x893/Thingy52/documentation/dfu_mode.png

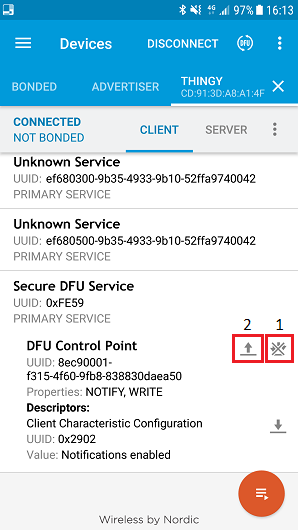
documentation/dfu_mode.png
