x893/Thingy52/documentation/distribution_packet.png

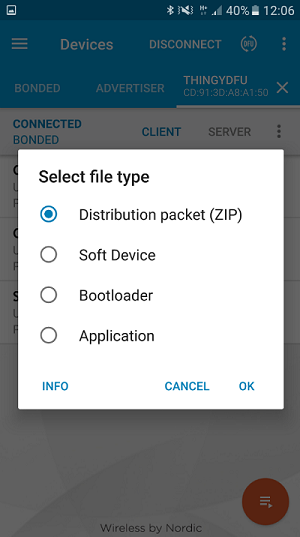
documentation/distribution_packet.png
