x893/Thingy52/documentation/fe59.png

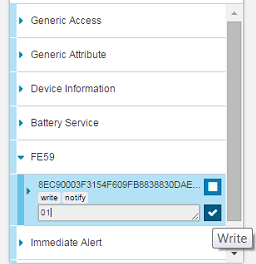
documentation/fe59.png
