x893/Thingy52/documentation/firmware_cable.png

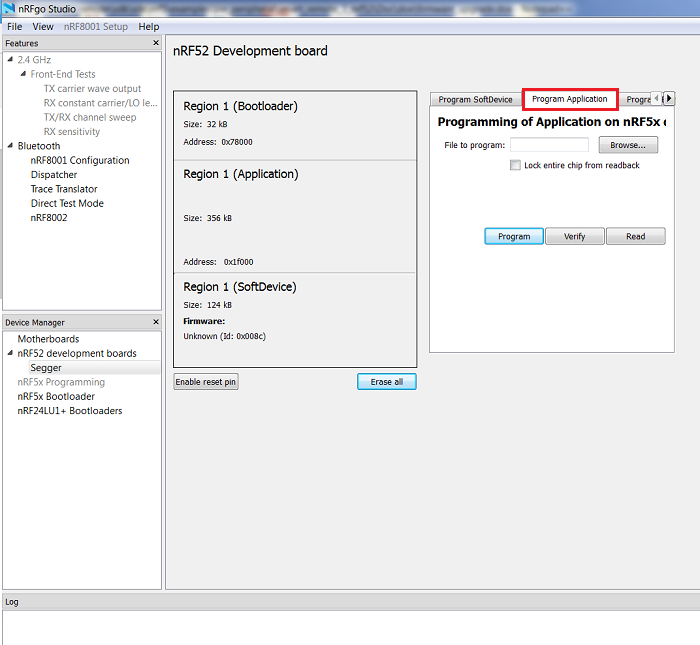
documentation/firmware_cable.png
