x893/Thingy52/documentation/firmware_update.png

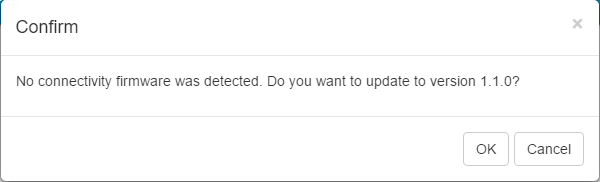
documentation/firmware_update.png
