x893/Thingy52/documentation/keil1.png

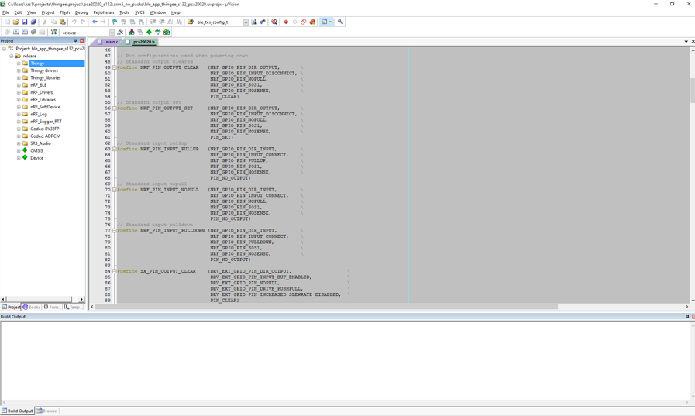
documentation/keil1.png
