x893/Thingy52/documentation/thingy_firmware_arch.png

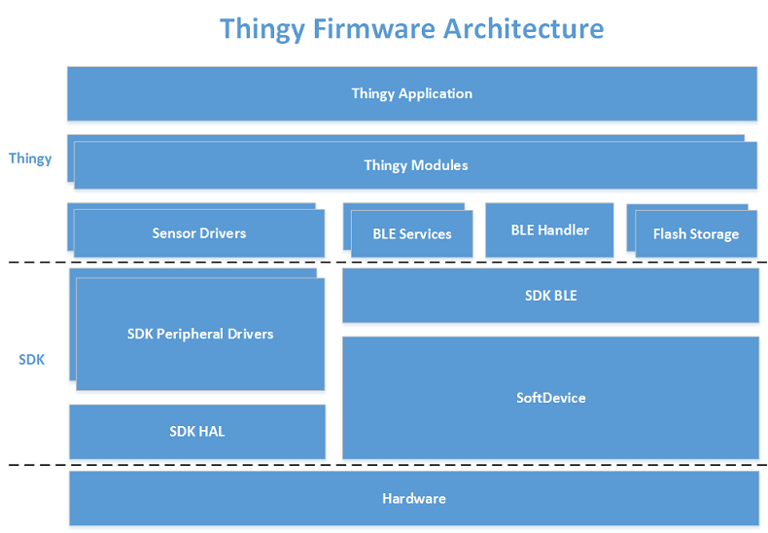
documentation/thingy_firmware_arch.png
