x893/Thingy52/sdk_components/drivers_nrf/uart/nrf_drv_uart.h

#define NRF_DRV_UART_H
#include "nrf_uart.h"
#ifdef UARTE_PRESENT
#include "nrf_uarte.h"
#endif
#include "sdk_errors.h"
#include "sdk_config.h"
#ifdef __cplusplus
extern "C" {
#endif
#define UART0_INSTANCE_INDEX 0
#define UART_COUNT 1
#if defined(UARTE_PRESENT)
    #define NRF_DRV_UART_PERIPHERAL(id)           \
        (CONCAT_3(UART, id, _CONFIG_USE_EASY_DMA) == 1 ? \
            (void *)CONCAT_2(NRF_UARTE, id)       \
          : (void *)CONCAT_2(NRF_UART, id))
#else
    #define NRF_DRV_UART_PERIPHERAL(id)  (void *)CONCAT_2(NRF_UART, id)
#endif
#if defined(UARTE_PRESENT)
#if (UART_EASY_DMA_SUPPORT == 1)
#define UARTE_IN_USE
#endif
#if (UART_LEGACY_SUPPORT == 1)
#define UART_IN_USE
#endif
#if (UART_ENABLED == 1) && ((!defined(UARTE_IN_USE) && !defined(UART_IN_USE)) || ((UART_EASY_DMA_SUPPORT == 0) && (UART_LEGACY_SUPPORT == 0)))
#error "Illegal settings in uart module!"
#endif
#elif defined(UART_PRESENT)
#define UART_IN_USE
#endif
typedef struct
{
    union
    {
#if (defined(UARTE_IN_USE))
    NRF_UARTE_Type * p_uarte; ///< Pointer to a structure with UARTE registers.
#endif
#if (defined(UART_IN_USE) || (UART_ENABLED == 0))
    NRF_UART_Type * p_uart;   ///< Pointer to a structure with UART registers.
#endif
    } reg;
    uint8_t drv_inst_idx;     ///< Driver instance index.
} nrf_drv_uart_t;
#define NRF_DRV_UART_INSTANCE(id)                            \
{                                                            \
    .reg          = {NRF_DRV_UART_PERIPHERAL(id)},           \
    .drv_inst_idx = CONCAT_3(UART, id, _INSTANCE_INDEX),\
}
typedef enum
{
    NRF_DRV_UART_EVT_TX_DONE, ///< Requested TX transfer completed.
    NRF_DRV_UART_EVT_RX_DONE, ///< Requested RX transfer completed.
    NRF_DRV_UART_EVT_ERROR,   ///< Error reported by UART peripheral.
} nrf_drv_uart_evt_type_t;
typedef struct
{
    uint32_t            pseltxd;            ///< TXD pin number.
    uint32_t            pselrxd;            ///< RXD pin number.
    uint32_t            pselcts;            ///< CTS pin number.
    uint32_t            pselrts;            ///< RTS pin number.
    void *              p_context;          ///< Context passed to interrupt handler.
    nrf_uart_hwfc_t     hwfc;               ///< Flow control configuration.
    nrf_uart_parity_t   parity;             ///< Parity configuration.
    nrf_uart_baudrate_t baudrate;           ///< Baudrate.
    uint8_t             interrupt_priority; ///< Interrupt priority.
#ifdef UARTE_PRESENT
    bool                use_easy_dma;
#endif
} nrf_drv_uart_config_t;
#ifdef UARTE_PRESENT
#if !UART_LEGACY_SUPPORT
#define DEFAULT_CONFIG_USE_EASY_DMA true
#elif !UART_EASY_DMA_SUPPORT
#define DEFAULT_CONFIG_USE_EASY_DMA false
#else
#define DEFAULT_CONFIG_USE_EASY_DMA UART0_USE_EASY_DMA
#endif
#define NRF_DRV_UART_DEFAULT_CONFIG                                                   \
    {                                                                                 \
        .pseltxd            = NRF_UART_PSEL_DISCONNECTED,                             \
        .pselrxd            = NRF_UART_PSEL_DISCONNECTED,                             \
        .pselcts            = NRF_UART_PSEL_DISCONNECTED,                             \
        .pselrts            = NRF_UART_PSEL_DISCONNECTED,                             \
        .p_context          = NULL,                                                   \
        .hwfc               = (nrf_uart_hwfc_t)UART_DEFAULT_CONFIG_HWFC,              \
        .parity             = (nrf_uart_parity_t)UART_DEFAULT_CONFIG_PARITY,          \
        .baudrate           = (nrf_uart_baudrate_t)UART_DEFAULT_CONFIG_BAUDRATE,      \
        .interrupt_priority = UART_DEFAULT_CONFIG_IRQ_PRIORITY,                       \
        .use_easy_dma       = true                                                    \
    }
#else
#define NRF_DRV_UART_DEFAULT_CONFIG                                                   \
    {                                                                                 \
        .pseltxd            = NRF_UART_PSEL_DISCONNECTED,                             \
        .pselrxd            = NRF_UART_PSEL_DISCONNECTED,                             \
        .pselcts            = NRF_UART_PSEL_DISCONNECTED,                             \
        .pselrts            = NRF_UART_PSEL_DISCONNECTED,                             \
        .p_context          = NULL,                                                   \
        .hwfc               = (nrf_uart_hwfc_t)UART_DEFAULT_CONFIG_HWFC,              \
        .parity             = (nrf_uart_parity_t)UART_DEFAULT_CONFIG_PARITY,          \
        .baudrate           = (nrf_uart_baudrate_t)UART_DEFAULT_CONFIG_BAUDRATE,      \
        .interrupt_priority = UART_DEFAULT_CONFIG_IRQ_PRIORITY,                       \
    }
#endif
typedef struct
{
    uint8_t * p_data; ///< Pointer to memory used for transfer.
    uint8_t   bytes;  ///< Number of bytes transfered.
} nrf_drv_uart_xfer_evt_t;
typedef struct
{
    nrf_drv_uart_xfer_evt_t rxtx;      ///< Transfer details includes number of bytes transfered.
    uint32_t                error_mask;///< Mask of error flags that generated the event.
} nrf_drv_uart_error_evt_t;
typedef struct
{
    nrf_drv_uart_evt_type_t type;      ///< Event type.
    union
    {
        nrf_drv_uart_xfer_evt_t  rxtx; ///< Data provided for transfer completion events.
        nrf_drv_uart_error_evt_t error;///< Data provided for error event.
    } data;
} nrf_drv_uart_event_t;
typedef void (*nrf_uart_event_handler_t)(nrf_drv_uart_event_t * p_event, void * p_context);
ret_code_t nrf_drv_uart_init(nrf_drv_uart_t const *        p_instance,
                             nrf_drv_uart_config_t const * p_config,
                             nrf_uart_event_handler_t      event_handler);
void nrf_drv_uart_uninit(nrf_drv_uart_t const * p_instance);
__STATIC_INLINE uint32_t nrf_drv_uart_task_address_get(nrf_drv_uart_t const * p_instance,
                                                       nrf_uart_task_t task);
__STATIC_INLINE uint32_t nrf_drv_uart_event_address_get(nrf_drv_uart_t const * p_instance,
                                                        nrf_uart_event_t event);
ret_code_t nrf_drv_uart_tx(nrf_drv_uart_t const * p_instance,
                           uint8_t const * const p_data, uint8_t length);
bool nrf_drv_uart_tx_in_progress(nrf_drv_uart_t const * p_instance);
void nrf_drv_uart_tx_abort(nrf_drv_uart_t const * p_instance);
ret_code_t nrf_drv_uart_rx(nrf_drv_uart_t const * p_instance,
                           uint8_t * p_data, uint8_t length);
void nrf_drv_uart_rx_enable(nrf_drv_uart_t const * p_instance);
void nrf_drv_uart_rx_disable(nrf_drv_uart_t const * p_instance);
void nrf_drv_uart_rx_abort(nrf_drv_uart_t const * p_instance);
uint32_t nrf_drv_uart_errorsrc_get(nrf_drv_uart_t const * p_instance);
#ifndef SUPPRESS_INLINE_IMPLEMENTATION
__STATIC_INLINE uint32_t nrf_drv_uart_task_address_get(nrf_drv_uart_t const * p_instance,
                                                       nrf_uart_task_t task)
{
#ifdef UART_IN_USE
    return nrf_uart_task_address_get(p_instance->reg.p_uart, task);
#else
    return nrf_uarte_task_address_get(p_instance->reg.p_uarte, (nrf_uarte_task_t)task);
#endif
}
__STATIC_INLINE uint32_t nrf_drv_uart_event_address_get(nrf_drv_uart_t const * p_instance,
                                                        nrf_uart_event_t event)
{
#ifdef UART_IN_USE
    return nrf_uart_event_address_get(p_instance->reg.p_uart, event);
#else
    return nrf_uarte_event_address_get(p_instance->reg.p_uarte, (nrf_uarte_event_t)event);
#endif
}
#endif //SUPPRESS_INLINE_IMPLEMENTATION
#ifdef __cplusplus
}
#endif
