x893/Thingy52/include/drivers/drv_sx1509_bitfields.h

/*
  Copyright (c) 2010 - 2017, Nordic Semiconductor ASA
  All rights reserved.

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
  1. Redistributions of source code must retain the above copyright notice, this
     list of conditions and the following disclaimer.

  2. Redistributions in binary form, except as embedded into a Nordic
     Semiconductor ASA integrated circuit in a product or a software update for
     such product, must reproduce the above copyright notice, this list of
     conditions and the following disclaimer in the documentation and/or other
     materials provided with the distribution.

  3. Neither the name of Nordic Semiconductor ASA nor the names of its
     contributors may be used to endorse or promote products derived from this
     software without specific prior written permission.

  4. This software, with or without modification, must only be used with a
     Nordic Semiconductor ASA integrated circuit.

  5. Any software provided in binary form under this license must not be reverse
     engineered, decompiled, modified and/or disassembled.

  THIS SOFTWARE IS PROVIDED BY NORDIC SEMICONDUCTOR ASA "AS IS" AND ANY EXPRESS
  OR IMPLIED WARRANTIES, INCLUDING, BUT NOT LIMITED TO, THE IMPLIED WARRANTIES
  OF MERCHANTABILITY, NONINFRINGEMENT, AND FITNESS FOR A PARTICULAR PURPOSE ARE
  DISCLAIMED. IN NO EVENT SHALL NORDIC SEMICONDUCTOR ASA OR CONTRIBUTORS BE
  LIABLE FOR ANY DIRECT, INDIRECT, INCIDENTAL, SPECIAL, EXEMPLARY, OR
  CONSEQUENTIAL DAMAGES (INCLUDING, BUT NOT LIMITED TO, PROCUREMENT OF SUBSTITUTE
  GOODS OR SERVICES; LOSS OF USE, DATA, OR PROFITS; OR BUSINESS INTERRUPTION)
  HOWEVER CAUSED AND ON ANY THEORY OF LIABILITY, WHETHER IN CONTRACT, STRICT
  LIABILITY, OR TORT (INCLUDING NEGLIGENCE OR OTHERWISE) ARISING IN ANY WAY OUT
  OF THE USE OF THIS SOFTWARE, EVEN IF ADVISED OF THE POSSIBILITY OF SUCH DAMAGE.
 */

#ifndef DRV_SX1509_BITFIELDS_H__
#define DRV_SX1509_BITFIELDS_H__

#define DRV_SX1509_FADE_SUPPORTED_PORT_MASK (0xF0F0)

/* Register: INPBUFDISABLE. */
/* Description: Input buffer disable register. */


/* Field INPBUF15: Disables/Enables the input buffer of the I/O pin. */
#define DRV_SX1509_INPBUFDISABLE_INPBUF15_Pos      (15)                                           /*!< The position of the field. */
#define DRV_SX1509_INPBUFDISABLE_INPBUF15_Msk      (0x1 << DRV_SX1509_INPBUFDISABLE_INPBUF15_Pos) /*!< The mask of the field. */
#define DRV_SX1509_INPBUFDISABLE_INPBUF15_Disabled (0)                                            /*!< Input buffer is disabled (input actually not being used, LED connection). */
#define DRV_SX1509_INPBUFDISABLE_INPBUF15_Enabled  (1)                                            /*!< Input buffer is enabled (input actually being used). */


/* Field INPBUF14: Disables/Enables the input buffer of the I/O pin. */
#define DRV_SX1509_INPBUFDISABLE_INPBUF14_Pos      (14)                                           /*!< The position of the field. */
#define DRV_SX1509_INPBUFDISABLE_INPBUF14_Msk      (0x1 << DRV_SX1509_INPBUFDISABLE_INPBUF14_Pos) /*!< The mask of the field. */
#define DRV_SX1509_INPBUFDISABLE_INPBUF14_Disabled (0)                                            /*!< Input buffer is disabled (input actually not being used, LED connection). */
#define DRV_SX1509_INPBUFDISABLE_INPBUF14_Enabled  (1)                                            /*!< Input buffer is enabled (input actually being used). */


/* Field INPBUF13: Disables/Enables the input buffer of the I/O pin. */
#define DRV_SX1509_INPBUFDISABLE_INPBUF13_Pos      (13)                                           /*!< The position of the field. */
#define DRV_SX1509_INPBUFDISABLE_INPBUF13_Msk      (0x1 << DRV_SX1509_INPBUFDISABLE_INPBUF13_Pos) /*!< The mask of the field. */
#define DRV_SX1509_INPBUFDISABLE_INPBUF13_Disabled (0)                                            /*!< Input buffer is disabled (input actually not being used, LED connection). */
#define DRV_SX1509_INPBUFDISABLE_INPBUF13_Enabled  (1)                                            /*!< Input buffer is enabled (input actually being used). */


/* Field INPBUF12: Disables/Enables the input buffer of the I/O pin. */
#define DRV_SX1509_INPBUFDISABLE_INPBUF12_Pos      (12)                                           /*!< The position of the field. */
#define DRV_SX1509_INPBUFDISABLE_INPBUF12_Msk      (0x1 << DRV_SX1509_INPBUFDISABLE_INPBUF12_Pos) /*!< The mask of the field. */
#define DRV_SX1509_INPBUFDISABLE_INPBUF12_Disabled (0)                                            /*!< Input buffer is disabled (input actually not being used, LED connection). */
#define DRV_SX1509_INPBUFDISABLE_INPBUF12_Enabled  (1)                                            /*!< Input buffer is enabled (input actually being used). */


/* Field INPBUF11: Disables/Enables the input buffer of the I/O pin. */
#define DRV_SX1509_INPBUFDISABLE_INPBUF11_Pos      (11)                                           /*!< The position of the field. */
#define DRV_SX1509_INPBUFDISABLE_INPBUF11_Msk      (0x1 << DRV_SX1509_INPBUFDISABLE_INPBUF11_Pos) /*!< The mask of the field. */
#define DRV_SX1509_INPBUFDISABLE_INPBUF11_Disabled (0)                                            /*!< Input buffer is disabled (input actually not being used, LED connection). */
#define DRV_SX1509_INPBUFDISABLE_INPBUF11_Enabled  (1)                                            /*!< Input buffer is enabled (input actually being used). */


/* Field INPBUF10: Disables/Enables the input buffer of the I/O pin. */
#define DRV_SX1509_INPBUFDISABLE_INPBUF10_Pos      (10)                                           /*!< The position of the field. */
#define DRV_SX1509_INPBUFDISABLE_INPBUF10_Msk      (0x1 << DRV_SX1509_INPBUFDISABLE_INPBUF10_Pos) /*!< The mask of the field. */
#define DRV_SX1509_INPBUFDISABLE_INPBUF10_Disabled (0)                                            /*!< Input buffer is disabled (input actually not being used, LED connection). */
#define DRV_SX1509_INPBUFDISABLE_INPBUF10_Enabled  (1)                                            /*!< Input buffer is enabled (input actually being used). */


/* Field INPBUF9: Disables/Enables the input buffer of the I/O pin. */
#define DRV_SX1509_INPBUFDISABLE_INPBUF9_Pos      (9)                                           /*!< The position of the field. */
#define DRV_SX1509_INPBUFDISABLE_INPBUF9_Msk      (0x1 << DRV_SX1509_INPBUFDISABLE_INPBUF9_Pos) /*!< The mask of the field. */
#define DRV_SX1509_INPBUFDISABLE_INPBUF9_Disabled (0)                                           /*!< Input buffer is disabled (input actually not being used, LED connection). */
#define DRV_SX1509_INPBUFDISABLE_INPBUF9_Enabled  (1)                                           /*!< Input buffer is enabled (input actually being used). */


/* Field INPBUF8: Disables/Enables the input buffer of the I/O pin. */
#define DRV_SX1509_INPBUFDISABLE_INPBUF8_Pos      (8)                                           /*!< The position of the field. */
#define DRV_SX1509_INPBUFDISABLE_INPBUF8_Msk      (0x1 << DRV_SX1509_INPBUFDISABLE_INPBUF8_Pos) /*!< The mask of the field. */
#define DRV_SX1509_INPBUFDISABLE_INPBUF8_Disabled (0)                                           /*!< Input buffer is disabled (input actually not being used, LED connection). */
#define DRV_SX1509_INPBUFDISABLE_INPBUF8_Enabled  (1)                                           /*!< Input buffer is enabled (input actually being used). */


/* Field INPBUF7: Disables/Enables the input buffer of the I/O pin. */
#define DRV_SX1509_INPBUFDISABLE_INPBUF7_Pos      (7)                                           /*!< The position of the field. */
#define DRV_SX1509_INPBUFDISABLE_INPBUF7_Msk      (0x1 << DRV_SX1509_INPBUFDISABLE_INPBUF7_Pos) /*!< The mask of the field. */
#define DRV_SX1509_INPBUFDISABLE_INPBUF7_Disabled (0)                                           /*!< Input buffer is disabled (input actually not being used, LED connection). */
#define DRV_SX1509_INPBUFDISABLE_INPBUF7_Enabled  (1)                                           /*!< Input buffer is enabled (input actually being used). */


/* Field INPBUF6: Disables/Enables the input buffer of the I/O pin. */
#define DRV_SX1509_INPBUFDISABLE_INPBUF6_Pos      (6)                                           /*!< The position of the field. */
#define DRV_SX1509_INPBUFDISABLE_INPBUF6_Msk      (0x1 << DRV_SX1509_INPBUFDISABLE_INPBUF6_Pos) /*!< The mask of the field. */
#define DRV_SX1509_INPBUFDISABLE_INPBUF6_Disabled (0)                                           /*!< Input buffer is disabled (input actually not being used, LED connection). */
#define DRV_SX1509_INPBUFDISABLE_INPBUF6_Enabled  (1)                                           /*!< Input buffer is enabled (input actually being used). */


/* Field INPBUF5: Disables/Enables the input buffer of the I/O pin. */
#define DRV_SX1509_INPBUFDISABLE_INPBUF5_Pos      (5)                                           /*!< The position of the field. */
#define DRV_SX1509_INPBUFDISABLE_INPBUF5_Msk      (0x1 << DRV_SX1509_INPBUFDISABLE_INPBUF5_Pos) /*!< The mask of the field. */
#define DRV_SX1509_INPBUFDISABLE_INPBUF5_Disabled (0)                                           /*!< Input buffer is disabled (input actually not being used, LED connection). */
#define DRV_SX1509_INPBUFDISABLE_INPBUF5_Enabled  (1)                                           /*!< Input buffer is enabled (input actually being used). */


/* Field INPBUF4: Disables/Enables the input buffer of the I/O pin. */
#define DRV_SX1509_INPBUFDISABLE_INPBUF4_Pos      (4)                                           /*!< The position of the field. */
#define DRV_SX1509_INPBUFDISABLE_INPBUF4_Msk      (0x1 << DRV_SX1509_INPBUFDISABLE_INPBUF4_Pos) /*!< The mask of the field. */
#define DRV_SX1509_INPBUFDISABLE_INPBUF4_Disabled (0)                                           /*!< Input buffer is disabled (input actually not being used, LED connection). */
#define DRV_SX1509_INPBUFDISABLE_INPBUF4_Enabled  (1)                                           /*!< Input buffer is enabled (input actually being used). */


/* Field INPBUF3: Disables/Enables the input buffer of the I/O pin. */
#define DRV_SX1509_INPBUFDISABLE_INPBUF3_Pos      (3)                                           /*!< The position of the field. */
#define DRV_SX1509_INPBUFDISABLE_INPBUF3_Msk      (0x1 << DRV_SX1509_INPBUFDISABLE_INPBUF3_Pos) /*!< The mask of the field. */
#define DRV_SX1509_INPBUFDISABLE_INPBUF3_Disabled (0)                                           /*!< Input buffer is disabled (input actually not being used, LED connection). */
#define DRV_SX1509_INPBUFDISABLE_INPBUF3_Enabled  (1)                                           /*!< Input buffer is enabled (input actually being used). */


/* Field INPBUF2: Disables/Enables the input buffer of the I/O pin. */
#define DRV_SX1509_INPBUFDISABLE_INPBUF2_Pos      (2)                                           /*!< The position of the field. */
#define DRV_SX1509_INPBUFDISABLE_INPBUF2_Msk      (0x1 << DRV_SX1509_INPBUFDISABLE_INPBUF2_Pos) /*!< The mask of the field. */
#define DRV_SX1509_INPBUFDISABLE_INPBUF2_Disabled (0)                                           /*!< Input buffer is disabled (input actually not being used, LED connection). */
#define DRV_SX1509_INPBUFDISABLE_INPBUF2_Enabled  (1)                                           /*!< Input buffer is enabled (input actually being used). */


/* Field INPBUF1: Disables/Enables the input buffer of the I/O pin. */
#define DRV_SX1509_INPBUFDISABLE_INPBUF1_Pos      (1)                                           /*!< The position of the field. */
#define DRV_SX1509_INPBUFDISABLE_INPBUF1_Msk      (0x1 << DRV_SX1509_INPBUFDISABLE_INPBUF1_Pos) /*!< The mask of the field. */
#define DRV_SX1509_INPBUFDISABLE_INPBUF1_Disabled (0)                                           /*!< Input buffer is disabled (input actually not being used, LED connection). */
#define DRV_SX1509_INPBUFDISABLE_INPBUF1_Enabled  (1)                                           /*!< Input buffer is enabled (input actually being used). */


/* Field INPBUF0: Disables/Enables the input buffer of the I/O pin. */
#define DRV_SX1509_INPBUFDISABLE_INPBUF0_Pos      (0)                                           /*!< The position of the field. */
#define DRV_SX1509_INPBUFDISABLE_INPBUF0_Msk      (0x1 << DRV_SX1509_INPBUFDISABLE_INPBUF0_Pos) /*!< The mask of the field. */
#define DRV_SX1509_INPBUFDISABLE_INPBUF0_Disabled (0)                                           /*!< Input buffer is disabled (input actually not being used, LED connection). */
#define DRV_SX1509_INPBUFDISABLE_INPBUF0_Enabled  (1)                                           /*!< Input buffer is enabled (input actually being used). */


/* Register: LONGSLEWRATE. */
/* Description: Output buffer long slew register. */


/* Field PIN15: Enables/Disables increased slew rate of the output buffer of each [output-configured] IO. */
#define DRV_SX1509_LONGSLEWRATE_PIN15_Pos      (15)                                       /*!< The position of the field. */
#define DRV_SX1509_LONGSLEWRATE_PIN15_Msk      (0x1 << DRV_SX1509_LONGSLEWRATE_PIN15_Pos) /*!< The mask of the field. */
#define DRV_SX1509_LONGSLEWRATE_PIN15_Disabled (0)                                        /*!< Increased slew rate is disabled. */
#define DRV_SX1509_LONGSLEWRATE_PIN15_Enabled  (1)                                        /*!< Increased slew rate is enabled. */


/* Field PIN14: Enables/Disables increased slew rate of the output buffer of each [output-configured] IO. */
#define DRV_SX1509_LONGSLEWRATE_PIN14_Pos      (14)                                       /*!< The position of the field. */
#define DRV_SX1509_LONGSLEWRATE_PIN14_Msk      (0x1 << DRV_SX1509_LONGSLEWRATE_PIN14_Pos) /*!< The mask of the field. */
#define DRV_SX1509_LONGSLEWRATE_PIN14_Disabled (0)                                        /*!< Increased slew rate is disabled. */
#define DRV_SX1509_LONGSLEWRATE_PIN14_Enabled  (1)                                        /*!< Increased slew rate is enabled. */


/* Field PIN13: Enables/Disables increased slew rate of the output buffer of each [output-configured] IO. */
#define DRV_SX1509_LONGSLEWRATE_PIN13_Pos      (13)                                       /*!< The position of the field. */
#define DRV_SX1509_LONGSLEWRATE_PIN13_Msk      (0x1 << DRV_SX1509_LONGSLEWRATE_PIN13_Pos) /*!< The mask of the field. */
#define DRV_SX1509_LONGSLEWRATE_PIN13_Disabled (0)                                        /*!< Increased slew rate is disabled. */
#define DRV_SX1509_LONGSLEWRATE_PIN13_Enabled  (1)                                        /*!< Increased slew rate is enabled. */


/* Field PIN12: Enables/Disables increased slew rate of the output buffer of each [output-configured] IO. */
#define DRV_SX1509_LONGSLEWRATE_PIN12_Pos      (12)                                       /*!< The position of the field. */
#define DRV_SX1509_LONGSLEWRATE_PIN12_Msk      (0x1 << DRV_SX1509_LONGSLEWRATE_PIN12_Pos) /*!< The mask of the field. */
#define DRV_SX1509_LONGSLEWRATE_PIN12_Disabled (0)                                        /*!< Increased slew rate is disabled. */
#define DRV_SX1509_LONGSLEWRATE_PIN12_Enabled  (1)                                        /*!< Increased slew rate is enabled. */


/* Field PIN11: Enables/Disables increased slew rate of the output buffer of each [output-configured] IO. */
#define DRV_SX1509_LONGSLEWRATE_PIN11_Pos      (11)                                       /*!< The position of the field. */
#define DRV_SX1509_LONGSLEWRATE_PIN11_Msk      (0x1 << DRV_SX1509_LONGSLEWRATE_PIN11_Pos) /*!< The mask of the field. */
#define DRV_SX1509_LONGSLEWRATE_PIN11_Disabled (0)                                        /*!< Increased slew rate is disabled. */
#define DRV_SX1509_LONGSLEWRATE_PIN11_Enabled  (1)                                        /*!< Increased slew rate is enabled. */


/* Field PIN10: Enables/Disables increased slew rate of the output buffer of each [output-configured] IO. */
#define DRV_SX1509_LONGSLEWRATE_PIN10_Pos      (10)                                       /*!< The position of the field. */
#define DRV_SX1509_LONGSLEWRATE_PIN10_Msk      (0x1 << DRV_SX1509_LONGSLEWRATE_PIN10_Pos) /*!< The mask of the field. */
#define DRV_SX1509_LONGSLEWRATE_PIN10_Disabled (0)                                        /*!< Increased slew rate is disabled. */
#define DRV_SX1509_LONGSLEWRATE_PIN10_Enabled  (1)                                        /*!< Increased slew rate is enabled. */


/* Field PIN9: Enables/Disables increased slew rate of the output buffer of each [output-configured] IO. */
#define DRV_SX1509_LONGSLEWRATE_PIN9_Pos      (9)                                       /*!< The position of the field. */
#define DRV_SX1509_LONGSLEWRATE_PIN9_Msk      (0x1 << DRV_SX1509_LONGSLEWRATE_PIN9_Pos) /*!< The mask of the field. */
#define DRV_SX1509_LONGSLEWRATE_PIN9_Disabled (0)                                       /*!< Increased slew rate is disabled. */
#define DRV_SX1509_LONGSLEWRATE_PIN9_Enabled  (1)                                       /*!< Increased slew rate is enabled. */


/* Field PIN8: Enables/Disables increased slew rate of the output buffer of each [output-configured] IO. */
#define DRV_SX1509_LONGSLEWRATE_PIN8_Pos      (8)                                       /*!< The position of the field. */
#define DRV_SX1509_LONGSLEWRATE_PIN8_Msk      (0x1 << DRV_SX1509_LONGSLEWRATE_PIN8_Pos) /*!< The mask of the field. */
#define DRV_SX1509_LONGSLEWRATE_PIN8_Disabled (0)                                       /*!< Increased slew rate is disabled. */
#define DRV_SX1509_LONGSLEWRATE_PIN8_Enabled  (1)                                       /*!< Increased slew rate is enabled. */


/* Field PIN7: Enables/Disables increased slew rate of the output buffer of each [output-configured] IO. */
#define DRV_SX1509_LONGSLEWRATE_PIN7_Pos      (7)                                       /*!< The position of the field. */
#define DRV_SX1509_LONGSLEWRATE_PIN7_Msk      (0x1 << DRV_SX1509_LONGSLEWRATE_PIN7_Pos) /*!< The mask of the field. */
#define DRV_SX1509_LONGSLEWRATE_PIN7_Disabled (0)                                       /*!< Increased slew rate is disabled. */
#define DRV_SX1509_LONGSLEWRATE_PIN7_Enabled  (1)                                       /*!< Increased slew rate is enabled. */


/* Field PIN6: Enables/Disables increased slew rate of the output buffer of each [output-configured] IO. */
#define DRV_SX1509_LONGSLEWRATE_PIN6_Pos      (6)                                       /*!< The position of the field. */
#define DRV_SX1509_LONGSLEWRATE_PIN6_Msk      (0x1 << DRV_SX1509_LONGSLEWRATE_PIN6_Pos) /*!< The mask of the field. */
#define DRV_SX1509_LONGSLEWRATE_PIN6_Disabled (0)                                       /*!< Increased slew rate is disabled. */
#define DRV_SX1509_LONGSLEWRATE_PIN6_Enabled  (1)                                       /*!< Increased slew rate is enabled. */


/* Field PIN5: Enables/Disables increased slew rate of the output buffer of each [output-configured] IO. */
#define DRV_SX1509_LONGSLEWRATE_PIN5_Pos      (5)                                       /*!< The position of the field. */
#define DRV_SX1509_LONGSLEWRATE_PIN5_Msk      (0x1 << DRV_SX1509_LONGSLEWRATE_PIN5_Pos) /*!< The mask of the field. */
#define DRV_SX1509_LONGSLEWRATE_PIN5_Disabled (0)                                       /*!< Increased slew rate is disabled. */
#define DRV_SX1509_LONGSLEWRATE_PIN5_Enabled  (1)                                       /*!< Increased slew rate is enabled. */


/* Field PIN4: Enables/Disables increased slew rate of the output buffer of each [output-configured] IO. */
#define DRV_SX1509_LONGSLEWRATE_PIN4_Pos      (4)                                       /*!< The position of the field. */
#define DRV_SX1509_LONGSLEWRATE_PIN4_Msk      (0x1 << DRV_SX1509_LONGSLEWRATE_PIN4_Pos) /*!< The mask of the field. */
#define DRV_SX1509_LONGSLEWRATE_PIN4_Disabled (0)                                       /*!< Increased slew rate is disabled. */
#define DRV_SX1509_LONGSLEWRATE_PIN4_Enabled  (1)                                       /*!< Increased slew rate is enabled. */


/* Field PIN3: Enables/Disables increased slew rate of the output buffer of each [output-configured] IO. */
#define DRV_SX1509_LONGSLEWRATE_PIN3_Pos      (3)                                       /*!< The position of the field. */
#define DRV_SX1509_LONGSLEWRATE_PIN3_Msk      (0x1 << DRV_SX1509_LONGSLEWRATE_PIN3_Pos) /*!< The mask of the field. */
#define DRV_SX1509_LONGSLEWRATE_PIN3_Disabled (0)                                       /*!< Increased slew rate is disabled. */
#define DRV_SX1509_LONGSLEWRATE_PIN3_Enabled  (1)                                       /*!< Increased slew rate is enabled. */


/* Field PIN2: Enables/Disables increased slew rate of the output buffer of each [output-configured] IO. */
#define DRV_SX1509_LONGSLEWRATE_PIN2_Pos      (2)                                       /*!< The position of the field. */
#define DRV_SX1509_LONGSLEWRATE_PIN2_Msk      (0x1 << DRV_SX1509_LONGSLEWRATE_PIN2_Pos) /*!< The mask of the field. */
#define DRV_SX1509_LONGSLEWRATE_PIN2_Disabled (0)                                       /*!< Increased slew rate is disabled. */
#define DRV_SX1509_LONGSLEWRATE_PIN2_Enabled  (1)                                       /*!< Increased slew rate is enabled. */


/* Field PIN1: Enables/Disables increased slew rate of the output buffer of each [output-configured] IO. */
#define DRV_SX1509_LONGSLEWRATE_PIN1_Pos      (1)                                       /*!< The position of the field. */
#define DRV_SX1509_LONGSLEWRATE_PIN1_Msk      (0x1 << DRV_SX1509_LONGSLEWRATE_PIN1_Pos) /*!< The mask of the field. */
#define DRV_SX1509_LONGSLEWRATE_PIN1_Disabled (0)                                       /*!< Increased slew rate is disabled. */
#define DRV_SX1509_LONGSLEWRATE_PIN1_Enabled  (1)                                       /*!< Increased slew rate is enabled. */


/* Field PIN0: Enables/Disables increased slew rate of the output buffer of each [output-configured] IO. */
#define DRV_SX1509_LONGSLEWRATE_PIN0_Pos      (0)                                       /*!< The position of the field. */
#define DRV_SX1509_LONGSLEWRATE_PIN0_Msk      (0x1 << DRV_SX1509_LONGSLEWRATE_PIN0_Pos) /*!< The mask of the field. */
#define DRV_SX1509_LONGSLEWRATE_PIN0_Disabled (0)                                       /*!< Increased slew rate is disabled. */
#define DRV_SX1509_LONGSLEWRATE_PIN0_Enabled  (1)                                       /*!< Increased slew rate is enabled. */


/* Register: LOWDRIVE. */
/* Description: Output buffer low drive register. */


/* Field PIN15: Enables/Disables reduced drive of the output buffer of each [output-configured] IO. */
#define DRV_SX1509_LOWDRIVE_PIN15_Pos      (15)                                   /*!< The position of the field. */
#define DRV_SX1509_LOWDRIVE_PIN15_Msk      (0x1 << DRV_SX1509_LOWDRIVE_PIN15_Pos) /*!< The mask of the field. */
#define DRV_SX1509_LOWDRIVE_PIN15_Disabled (0)                                    /*!< Reduced drive is disabled. */
#define DRV_SX1509_LOWDRIVE_PIN15_Enabled  (1)                                    /*!< Reduced drive is enabled. */


/* Field PIN14: Enables/Disables reduced drive of the output buffer of each [output-configured] IO. */
#define DRV_SX1509_LOWDRIVE_PIN14_Pos      (14)                                   /*!< The position of the field. */
#define DRV_SX1509_LOWDRIVE_PIN14_Msk      (0x1 << DRV_SX1509_LOWDRIVE_PIN14_Pos) /*!< The mask of the field. */
#define DRV_SX1509_LOWDRIVE_PIN14_Disabled (0)                                    /*!< Reduced drive is disabled. */
#define DRV_SX1509_LOWDRIVE_PIN14_Enabled  (1)                                    /*!< Reduced drive is enabled. */


/* Field PIN13: Enables/Disables reduced drive of the output buffer of each [output-configured] IO. */
#define DRV_SX1509_LOWDRIVE_PIN13_Pos      (13)                                   /*!< The position of the field. */
#define DRV_SX1509_LOWDRIVE_PIN13_Msk      (0x1 << DRV_SX1509_LOWDRIVE_PIN13_Pos) /*!< The mask of the field. */
#define DRV_SX1509_LOWDRIVE_PIN13_Disabled (0)                                    /*!< Reduced drive is disabled. */
#define DRV_SX1509_LOWDRIVE_PIN13_Enabled  (1)                                    /*!< Reduced drive is enabled. */


/* Field PIN12: Enables/Disables reduced drive of the output buffer of each [output-configured] IO. */
#define DRV_SX1509_LOWDRIVE_PIN12_Pos      (12)                                   /*!< The position of the field. */
#define DRV_SX1509_LOWDRIVE_PIN12_Msk      (0x1 << DRV_SX1509_LOWDRIVE_PIN12_Pos) /*!< The mask of the field. */
#define DRV_SX1509_LOWDRIVE_PIN12_Disabled (0)                                    /*!< Reduced drive is disabled. */
#define DRV_SX1509_LOWDRIVE_PIN12_Enabled  (1)                                    /*!< Reduced drive is enabled. */


/* Field PIN11: Enables/Disables reduced drive of the output buffer of each [output-configured] IO. */
#define DRV_SX1509_LOWDRIVE_PIN11_Pos      (11)                                   /*!< The position of the field. */
#define DRV_SX1509_LOWDRIVE_PIN11_Msk      (0x1 << DRV_SX1509_LOWDRIVE_PIN11_Pos) /*!< The mask of the field. */
#define DRV_SX1509_LOWDRIVE_PIN11_Disabled (0)                                    /*!< Reduced drive is disabled. */
#define DRV_SX1509_LOWDRIVE_PIN11_Enabled  (1)                                    /*!< Reduced drive is enabled. */


/* Field PIN10: Enables/Disables reduced drive of the output buffer of each [output-configured] IO. */
#define DRV_SX1509_LOWDRIVE_PIN10_Pos      (10)                                   /*!< The position of the field. */
#define DRV_SX1509_LOWDRIVE_PIN10_Msk      (0x1 << DRV_SX1509_LOWDRIVE_PIN10_Pos) /*!< The mask of the field. */
#define DRV_SX1509_LOWDRIVE_PIN10_Disabled (0)                                    /*!< Reduced drive is disabled. */
#define DRV_SX1509_LOWDRIVE_PIN10_Enabled  (1)                                    /*!< Reduced drive is enabled. */


/* Field PIN9: Enables/Disables reduced drive of the output buffer of each [output-configured] IO. */
#define DRV_SX1509_LOWDRIVE_PIN9_Pos      (9)                                   /*!< The position of the field. */
#define DRV_SX1509_LOWDRIVE_PIN9_Msk      (0x1 << DRV_SX1509_LOWDRIVE_PIN9_Pos) /*!< The mask of the field. */
#define DRV_SX1509_LOWDRIVE_PIN9_Disabled (0)                                   /*!< Reduced drive is disabled. */
#define DRV_SX1509_LOWDRIVE_PIN9_Enabled  (1)                                   /*!< Reduced drive is enabled. */


/* Field PIN8: Enables/Disables reduced drive of the output buffer of each [output-configured] IO. */
#define DRV_SX1509_LOWDRIVE_PIN8_Pos      (8)                                   /*!< The position of the field. */
#define DRV_SX1509_LOWDRIVE_PIN8_Msk      (0x1 << DRV_SX1509_LOWDRIVE_PIN8_Pos) /*!< The mask of the field. */
#define DRV_SX1509_LOWDRIVE_PIN8_Disabled (0)                                   /*!< Reduced drive is disabled. */
#define DRV_SX1509_LOWDRIVE_PIN8_Enabled  (1)                                   /*!< Reduced drive is enabled. */


/* Field PIN7: Enables/Disables reduced drive of the output buffer of each [output-configured] IO. */
#define DRV_SX1509_LOWDRIVE_PIN7_Pos      (7)                                   /*!< The position of the field. */
#define DRV_SX1509_LOWDRIVE_PIN7_Msk      (0x1 << DRV_SX1509_LOWDRIVE_PIN7_Pos) /*!< The mask of the field. */
#define DRV_SX1509_LOWDRIVE_PIN7_Disabled (0)                                   /*!< Reduced drive is disabled. */
#define DRV_SX1509_LOWDRIVE_PIN7_Enabled  (1)                                   /*!< Reduced drive is enabled. */


/* Field PIN6: Enables/Disables reduced drive of the output buffer of each [output-configured] IO. */
#define DRV_SX1509_LOWDRIVE_PIN6_Pos      (6)                                   /*!< The position of the field. */
#define DRV_SX1509_LOWDRIVE_PIN6_Msk      (0x1 << DRV_SX1509_LOWDRIVE_PIN6_Pos) /*!< The mask of the field. */
#define DRV_SX1509_LOWDRIVE_PIN6_Disabled (0)                                   /*!< Reduced drive is disabled. */
#define DRV_SX1509_LOWDRIVE_PIN6_Enabled  (1)                                   /*!< Reduced drive is enabled. */


/* Field PIN5: Enables/Disables reduced drive of the output buffer of each [output-configured] IO. */
#define DRV_SX1509_LOWDRIVE_PIN5_Pos      (5)                                   /*!< The position of the field. */
#define DRV_SX1509_LOWDRIVE_PIN5_Msk      (0x1 << DRV_SX1509_LOWDRIVE_PIN5_Pos) /*!< The mask of the field. */
#define DRV_SX1509_LOWDRIVE_PIN5_Disabled (0)                                   /*!< Reduced drive is disabled. */
#define DRV_SX1509_LOWDRIVE_PIN5_Enabled  (1)                                   /*!< Reduced drive is enabled. */


/* Field PIN4: Enables/Disables reduced drive of the output buffer of each [output-configured] IO. */
#define DRV_SX1509_LOWDRIVE_PIN4_Pos      (4)                                   /*!< The position of the field. */
#define DRV_SX1509_LOWDRIVE_PIN4_Msk      (0x1 << DRV_SX1509_LOWDRIVE_PIN4_Pos) /*!< The mask of the field. */
#define DRV_SX1509_LOWDRIVE_PIN4_Disabled (0)                                   /*!< Reduced drive is disabled. */
#define DRV_SX1509_LOWDRIVE_PIN4_Enabled  (1)                                   /*!< Reduced drive is enabled. */


/* Field PIN3: Enables/Disables reduced drive of the output buffer of each [output-configured] IO. */
#define DRV_SX1509_LOWDRIVE_PIN3_Pos      (3)                                   /*!< The position of the field. */
#define DRV_SX1509_LOWDRIVE_PIN3_Msk      (0x1 << DRV_SX1509_LOWDRIVE_PIN3_Pos) /*!< The mask of the field. */
#define DRV_SX1509_LOWDRIVE_PIN3_Disabled (0)                                   /*!< Reduced drive is disabled. */
#define DRV_SX1509_LOWDRIVE_PIN3_Enabled  (1)                                   /*!< Reduced drive is enabled. */


/* Field PIN2: Enables/Disables reduced drive of the output buffer of each [output-configured] IO. */
#define DRV_SX1509_LOWDRIVE_PIN2_Pos      (2)                                   /*!< The position of the field. */
#define DRV_SX1509_LOWDRIVE_PIN2_Msk      (0x1 << DRV_SX1509_LOWDRIVE_PIN2_Pos) /*!< The mask of the field. */
#define DRV_SX1509_LOWDRIVE_PIN2_Disabled (0)                                   /*!< Reduced drive is disabled. */
#define DRV_SX1509_LOWDRIVE_PIN2_Enabled  (1)                                   /*!< Reduced drive is enabled. */


/* Field PIN1: Enables/Disables reduced drive of the output buffer of each [output-configured] IO. */
#define DRV_SX1509_LOWDRIVE_PIN1_Pos      (1)                                   /*!< The position of the field. */
#define DRV_SX1509_LOWDRIVE_PIN1_Msk      (0x1 << DRV_SX1509_LOWDRIVE_PIN1_Pos) /*!< The mask of the field. */
#define DRV_SX1509_LOWDRIVE_PIN1_Disabled (0)                                   /*!< Reduced drive is disabled. */
#define DRV_SX1509_LOWDRIVE_PIN1_Enabled  (1)                                   /*!< Reduced drive is enabled. */


/* Field PIN0: Enables/Disables reduced drive of the output buffer of each [output-configured] IO. */
#define DRV_SX1509_LOWDRIVE_PIN0_Pos      (0)                                   /*!< The position of the field. */
#define DRV_SX1509_LOWDRIVE_PIN0_Msk      (0x1 << DRV_SX1509_LOWDRIVE_PIN0_Pos) /*!< The mask of the field. */
#define DRV_SX1509_LOWDRIVE_PIN0_Disabled (0)                                   /*!< Reduced drive is disabled. */
#define DRV_SX1509_LOWDRIVE_PIN0_Enabled  (1)                                   /*!< Reduced drive is enabled. */


/* Register: PULLUP. */
/* Description: Pull-up register. */


/* Field PIN15: Enables/Disables the pull-up for each IO. */
#define DRV_SX1509_PULLUP_PIN15_Pos      (15)                                 /*!< The position of the field. */
#define DRV_SX1509_PULLUP_PIN15_Msk      (0x1 << DRV_SX1509_PULLUP_PIN15_Pos) /*!< The mask of the field. */
#define DRV_SX1509_PULLUP_PIN15_Disabled (0)                                  /*!< Pull-up is disabled. */
#define DRV_SX1509_PULLUP_PIN15_Enabled  (1)                                  /*!< Pull-up is enabled. */


/* Field PIN14: Enables/Disables the pull-up for each IO. */
#define DRV_SX1509_PULLUP_PIN14_Pos      (14)                                 /*!< The position of the field. */
#define DRV_SX1509_PULLUP_PIN14_Msk      (0x1 << DRV_SX1509_PULLUP_PIN14_Pos) /*!< The mask of the field. */
#define DRV_SX1509_PULLUP_PIN14_Disabled (0)                                  /*!< Pull-up is disabled. */
#define DRV_SX1509_PULLUP_PIN14_Enabled  (1)                                  /*!< Pull-up is enabled. */


/* Field PIN13: Enables/Disables the pull-up for each IO. */
#define DRV_SX1509_PULLUP_PIN13_Pos      (13)                                 /*!< The position of the field. */
#define DRV_SX1509_PULLUP_PIN13_Msk      (0x1 << DRV_SX1509_PULLUP_PIN13_Pos) /*!< The mask of the field. */
#define DRV_SX1509_PULLUP_PIN13_Disabled (0)                                  /*!< Pull-up is disabled. */
#define DRV_SX1509_PULLUP_PIN13_Enabled  (1)                                  /*!< Pull-up is enabled. */


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
#define DRV_SX1509_PULLUP_PIN4_Disabled (0)                                 /*!< Pull-up is disabled. */
#define DRV_SX1509_PULLUP_PIN4_Enabled  (1)                                 /*!< Pull-up is enabled. */


/* Field PIN3: Enables/Disables the pull-up for each IO. */
#define DRV_SX1509_PULLUP_PIN3_Pos      (3)                                 /*!< The position of the field. */
#define DRV_SX1509_PULLUP_PIN3_Msk      (0x1 << DRV_SX1509_PULLUP_PIN3_Pos) /*!< The mask of the field. */
#define DRV_SX1509_PULLUP_PIN3_Disabled (0)                                 /*!< Pull-up is disabled. */
#define DRV_SX1509_PULLUP_PIN3_Enabled  (1)                                 /*!< Pull-up is enabled. */


/* Field PIN2: Enables/Disables the pull-up for each IO. */
#define DRV_SX1509_PULLUP_PIN2_Pos      (2)                                 /*!< The position of the field. */
#define DRV_SX1509_PULLUP_PIN2_Msk      (0x1 << DRV_SX1509_PULLUP_PIN2_Pos) /*!< The mask of the field. */
#define DRV_SX1509_PULLUP_PIN2_Disabled (0)                                 /*!< Pull-up is disabled. */
#define DRV_SX1509_PULLUP_PIN2_Enabled  (1)                                 /*!< Pull-up is enabled. */


/* Field PIN1: Enables/Disables the pull-up for each IO. */
#define DRV_SX1509_PULLUP_PIN1_Pos      (1)                                 /*!< The position of the field. */
#define DRV_SX1509_PULLUP_PIN1_Msk      (0x1 << DRV_SX1509_PULLUP_PIN1_Pos) /*!< The mask of the field. */
#define DRV_SX1509_PULLUP_PIN1_Disabled (0)                                 /*!< Pull-up is disabled. */
#define DRV_SX1509_PULLUP_PIN1_Enabled  (1)                                 /*!< Pull-up is enabled. */


/* Field PIN0: Enables/Disables the pull-up for each IO. */
#define DRV_SX1509_PULLUP_PIN0_Pos      (0)                                 /*!< The position of the field. */
#define DRV_SX1509_PULLUP_PIN0_Msk      (0x1 << DRV_SX1509_PULLUP_PIN0_Pos) /*!< The mask of the field. */
#define DRV_SX1509_PULLUP_PIN0_Disabled (0)                                 /*!< Pull-up is disabled. */
#define DRV_SX1509_PULLUP_PIN0_Enabled  (1)                                 /*!< Pull-up is enabled. */


/* Register: PULLDOWN. */
/* Description: Pull-down register. */


/* Field PIN15: Enables/Disables pull-down for each IO. */
#define DRV_SX1509_PULLDOWN_PIN15_Pos      (15)                                   /*!< The position of the field. */
#define DRV_SX1509_PULLDOWN_PIN15_Msk      (0x1 << DRV_SX1509_PULLDOWN_PIN15_Pos) /*!< The mask of the field. */
#define DRV_SX1509_PULLDOWN_PIN15_Disabled (0)                                    /*!< Pull-down is disabled. */
#define DRV_SX1509_PULLDOWN_PIN15_Enabled  (1)                                    /*!< Pull-down is enabled. */


/* Field PIN14: Enables/Disables pull-down for each IO. */
#define DRV_SX1509_PULLDOWN_PIN14_Pos      (14)                                   /*!< The position of the field. */
#define DRV_SX1509_PULLDOWN_PIN14_Msk      (0x1 << DRV_SX1509_PULLDOWN_PIN14_Pos) /*!< The mask of the field. */
#define DRV_SX1509_PULLDOWN_PIN14_Disabled (0)                                    /*!< Pull-down is disabled. */
#define DRV_SX1509_PULLDOWN_PIN14_Enabled  (1)                                    /*!< Pull-down is enabled. */


/* Field PIN13: Enables/Disables pull-down for each IO. */
#define DRV_SX1509_PULLDOWN_PIN13_Pos      (13)                                   /*!< The position of the field. */
#define DRV_SX1509_PULLDOWN_PIN13_Msk      (0x1 << DRV_SX1509_PULLDOWN_PIN13_Pos) /*!< The mask of the field. */
#define DRV_SX1509_PULLDOWN_PIN13_Disabled (0)                                    /*!< Pull-down is disabled. */
#define DRV_SX1509_PULLDOWN_PIN13_Enabled  (1)                                    /*!< Pull-down is enabled. */


/* Field PIN12: Enables/Disables pull-down for each IO. */
#define DRV_SX1509_PULLDOWN_PIN12_Pos      (12)                                   /*!< The position of the field. */
#define DRV_SX1509_PULLDOWN_PIN12_Msk      (0x1 << DRV_SX1509_PULLDOWN_PIN12_Pos) /*!< The mask of the field. */
#define DRV_SX1509_PULLDOWN_PIN12_Disabled (0)                                    /*!< Pull-down is disabled. */
#define DRV_SX1509_PULLDOWN_PIN12_Enabled  (1)                                    /*!< Pull-down is enabled. */


/* Field PIN11: Enables/Disables pull-down for each IO. */
#define DRV_SX1509_PULLDOWN_PIN11_Pos      (11)                                   /*!< The position of the field. */
#define DRV_SX1509_PULLDOWN_PIN11_Msk      (0x1 << DRV_SX1509_PULLDOWN_PIN11_Pos) /*!< The mask of the field. */
#define DRV_SX1509_PULLDOWN_PIN11_Disabled (0)                                    /*!< Pull-down is disabled. */
#define DRV_SX1509_PULLDOWN_PIN11_Enabled  (1)                                    /*!< Pull-down is enabled. */


/* Field PIN10: Enables/Disables pull-down for each IO. */
#define DRV_SX1509_PULLDOWN_PIN10_Pos      (10)                                   /*!< The position of the field. */
#define DRV_SX1509_PULLDOWN_PIN10_Msk      (0x1 << DRV_SX1509_PULLDOWN_PIN10_Pos) /*!< The mask of the field. */
#define DRV_SX1509_PULLDOWN_PIN10_Disabled (0)                                    /*!< Pull-down is disabled. */
#define DRV_SX1509_PULLDOWN_PIN10_Enabled  (1)                                    /*!< Pull-down is enabled. */


/* Field PIN9: Enables/Disables pull-down for each IO. */
#define DRV_SX1509_PULLDOWN_PIN9_Pos      (9)                                   /*!< The position of the field. */
#define DRV_SX1509_PULLDOWN_PIN9_Msk      (0x1 << DRV_SX1509_PULLDOWN_PIN9_Pos) /*!< The mask of the field. */
#define DRV_SX1509_PULLDOWN_PIN9_Disabled (0)                                   /*!< Pull-down is disabled. */
#define DRV_SX1509_PULLDOWN_PIN9_Enabled  (1)                                   /*!< Pull-down is enabled. */


/* Field PIN8: Enables/Disables pull-down for each IO. */
#define DRV_SX1509_PULLDOWN_PIN8_Pos      (8)                                   /*!< The position of the field. */
#define DRV_SX1509_PULLDOWN_PIN8_Msk      (0x1 << DRV_SX1509_PULLDOWN_PIN8_Pos) /*!< The mask of the field. */
#define DRV_SX1509_PULLDOWN_PIN8_Disabled (0)                                   /*!< Pull-down is disabled. */
#define DRV_SX1509_PULLDOWN_PIN8_Enabled  (1)                                   /*!< Pull-down is enabled. */


/* Field PIN7: Enables/Disables pull-down for each IO. */
#define DRV_SX1509_PULLDOWN_PIN7_Pos      (7)                                   /*!< The position of the field. */
#define DRV_SX1509_PULLDOWN_PIN7_Msk      (0x1 << DRV_SX1509_PULLDOWN_PIN7_Pos) /*!< The mask of the field. */
#define DRV_SX1509_PULLDOWN_PIN7_Disabled (0)                                   /*!< Pull-down is disabled. */
#define DRV_SX1509_PULLDOWN_PIN7_Enabled  (1)                                   /*!< Pull-down is enabled. */


/* Field PIN6: Enables/Disables pull-down for each IO. */
#define DRV_SX1509_PULLDOWN_PIN6_Pos      (6)                                   /*!< The position of the field. */
#define DRV_SX1509_PULLDOWN_PIN6_Msk      (0x1 << DRV_SX1509_PULLDOWN_PIN6_Pos) /*!< The mask of the field. */
#define DRV_SX1509_PULLDOWN_PIN6_Disabled (0)                                   /*!< Pull-down is disabled. */
#define DRV_SX1509_PULLDOWN_PIN6_Enabled  (1)                                   /*!< Pull-down is enabled. */


/* Field PIN5: Enables/Disables pull-down for each IO. */
#define DRV_SX1509_PULLDOWN_PIN5_Pos      (5)                                   /*!< The position of the field. */
#define DRV_SX1509_PULLDOWN_PIN5_Msk      (0x1 << DRV_SX1509_PULLDOWN_PIN5_Pos) /*!< The mask of the field. */
#define DRV_SX1509_PULLDOWN_PIN5_Disabled (0)                                   /*!< Pull-down is disabled. */
#define DRV_SX1509_PULLDOWN_PIN5_Enabled  (1)                                   /*!< Pull-down is enabled. */


/* Field PIN4: Enables/Disables pull-down for each IO. */
#define DRV_SX1509_PULLDOWN_PIN4_Pos      (4)                                   /*!< The position of the field. */
#define DRV_SX1509_PULLDOWN_PIN4_Msk      (0x1 << DRV_SX1509_PULLDOWN_PIN4_Pos) /*!< The mask of the field. */
#define DRV_SX1509_PULLDOWN_PIN4_Disabled (0)                                   /*!< Pull-down is disabled. */
#define DRV_SX1509_PULLDOWN_PIN4_Enabled  (1)                                   /*!< Pull-down is enabled. */


/* Field PIN3: Enables/Disables pull-down for each IO. */
#define DRV_SX1509_PULLDOWN_PIN3_Pos      (3)                                   /*!< The position of the field. */
#define DRV_SX1509_PULLDOWN_PIN3_Msk      (0x1 << DRV_SX1509_PULLDOWN_PIN3_Pos) /*!< The mask of the field. */
#define DRV_SX1509_PULLDOWN_PIN3_Disabled (0)                                   /*!< Pull-down is disabled. */
#define DRV_SX1509_PULLDOWN_PIN3_Enabled  (1)                                   /*!< Pull-down is enabled. */


/* Field PIN2: Enables/Disables pull-down for each IO. */
#define DRV_SX1509_PULLDOWN_PIN2_Pos      (2)                                   /*!< The position of the field. */
#define DRV_SX1509_PULLDOWN_PIN2_Msk      (0x1 << DRV_SX1509_PULLDOWN_PIN2_Pos) /*!< The mask of the field. */
#define DRV_SX1509_PULLDOWN_PIN2_Disabled (0)                                   /*!< Pull-down is disabled. */
#define DRV_SX1509_PULLDOWN_PIN2_Enabled  (1)                                   /*!< Pull-down is enabled. */


/* Field PIN1: Enables/Disables pull-down for each IO. */
#define DRV_SX1509_PULLDOWN_PIN1_Pos      (1)                                   /*!< The position of the field. */
#define DRV_SX1509_PULLDOWN_PIN1_Msk      (0x1 << DRV_SX1509_PULLDOWN_PIN1_Pos) /*!< The mask of the field. */
#define DRV_SX1509_PULLDOWN_PIN1_Disabled (0)                                   /*!< Pull-down is disabled. */
#define DRV_SX1509_PULLDOWN_PIN1_Enabled  (1)                                   /*!< Pull-down is enabled. */


/* Field PIN0: Enables/Disables pull-down for each IO. */
#define DRV_SX1509_PULLDOWN_PIN0_Pos      (0)                                   /*!< The position of the field. */
#define DRV_SX1509_PULLDOWN_PIN0_Msk      (0x1 << DRV_SX1509_PULLDOWN_PIN0_Pos) /*!< The mask of the field. */
#define DRV_SX1509_PULLDOWN_PIN0_Disabled (0)                                   /*!< Pull-down is disabled. */
#define DRV_SX1509_PULLDOWN_PIN0_Enabled  (1)                                   /*!< Pull-down is enabled. */


/* Register: OPENDRAIN. */
/* Description: Enables/Disables open drain operation for each [output-configured] IO. */


/* Field PIN15: Enables/Disables open drain operation for each [output-configured] IO. */
#define DRV_SX1509_OPENDRAIN_PIN15_Pos       (15)                                    /*!< The position of the field. */
#define DRV_SX1509_OPENDRAIN_PIN15_Msk       (0x1 << DRV_SX1509_OPENDRAIN_PIN15_Pos) /*!< The mask of the field. */
#define DRV_SX1509_OPENDRAIN_PIN15_PushPull  (0)                                     /*!< Regular push-pull operation. */
#define DRV_SX1509_OPENDRAIN_PIN15_OpenDrain (1)                                     /*!< Open drain operation. */


/* Field PIN14: Enables/Disables open drain operation for each [output-configured] IO. */
#define DRV_SX1509_OPENDRAIN_PIN14_Pos       (14)                                    /*!< The position of the field. */
#define DRV_SX1509_OPENDRAIN_PIN14_Msk       (0x1 << DRV_SX1509_OPENDRAIN_PIN14_Pos) /*!< The mask of the field. */
#define DRV_SX1509_OPENDRAIN_PIN14_PushPull  (0)                                     /*!< Regular push-pull operation. */
#define DRV_SX1509_OPENDRAIN_PIN14_OpenDrain (1)                                     /*!< Open drain operation. */


/* Field PIN13: Enables/Disables open drain operation for each [output-configured] IO. */
#define DRV_SX1509_OPENDRAIN_PIN13_Pos       (13)                                    /*!< The position of the field. */
#define DRV_SX1509_OPENDRAIN_PIN13_Msk       (0x1 << DRV_SX1509_OPENDRAIN_PIN13_Pos) /*!< The mask of the field. */
#define DRV_SX1509_OPENDRAIN_PIN13_PushPull  (0)                                     /*!< Regular push-pull operation. */
#define DRV_SX1509_OPENDRAIN_PIN13_OpenDrain (1)                                     /*!< Open drain operation. */


/* Field PIN12: Enables/Disables open drain operation for each [output-configured] IO. */
#define DRV_SX1509_OPENDRAIN_PIN12_Pos       (12)                                    /*!< The position of the field. */
#define DRV_SX1509_OPENDRAIN_PIN12_Msk       (0x1 << DRV_SX1509_OPENDRAIN_PIN12_Pos) /*!< The mask of the field. */
#define DRV_SX1509_OPENDRAIN_PIN12_PushPull  (0)                                     /*!< Regular push-pull operation. */
#define DRV_SX1509_OPENDRAIN_PIN12_OpenDrain (1)                                     /*!< Open drain operation. */


/* Field PIN11: Enables/Disables open drain operation for each [output-configured] IO. */
#define DRV_SX1509_OPENDRAIN_PIN11_Pos       (11)                                    /*!< The position of the field. */
#define DRV_SX1509_OPENDRAIN_PIN11_Msk       (0x1 << DRV_SX1509_OPENDRAIN_PIN11_Pos) /*!< The mask of the field. */
#define DRV_SX1509_OPENDRAIN_PIN11_PushPull  (0)                                     /*!< Regular push-pull operation. */
#define DRV_SX1509_OPENDRAIN_PIN11_OpenDrain (1)                                     /*!< Open drain operation. */


/* Field PIN10: Enables/Disables open drain operation for each [output-configured] IO. */
#define DRV_SX1509_OPENDRAIN_PIN10_Pos       (10)                                    /*!< The position of the field. */
#define DRV_SX1509_OPENDRAIN_PIN10_Msk       (0x1 << DRV_SX1509_OPENDRAIN_PIN10_Pos) /*!< The mask of the field. */
#define DRV_SX1509_OPENDRAIN_PIN10_PushPull  (0)                                     /*!< Regular push-pull operation. */
#define DRV_SX1509_OPENDRAIN_PIN10_OpenDrain (1)                                     /*!< Open drain operation. */


/* Field PIN9: Enables/Disables open drain operation for each [output-configured] IO. */
#define DRV_SX1509_OPENDRAIN_PIN9_Pos       (9)                                    /*!< The position of the field. */
#define DRV_SX1509_OPENDRAIN_PIN9_Msk       (0x1 << DRV_SX1509_OPENDRAIN_PIN9_Pos) /*!< The mask of the field. */
#define DRV_SX1509_OPENDRAIN_PIN9_PushPull  (0)                                    /*!< Regular push-pull operation. */
#define DRV_SX1509_OPENDRAIN_PIN9_OpenDrain (1)                                    /*!< Open drain operation. */


/* Field PIN8: Enables/Disables open drain operation for each [output-configured] IO. */
#define DRV_SX1509_OPENDRAIN_PIN8_Pos       (8)                                    /*!< The position of the field. */
#define DRV_SX1509_OPENDRAIN_PIN8_Msk       (0x1 << DRV_SX1509_OPENDRAIN_PIN8_Pos) /*!< The mask of the field. */
#define DRV_SX1509_OPENDRAIN_PIN8_PushPull  (0)                                    /*!< Regular push-pull operation. */
#define DRV_SX1509_OPENDRAIN_PIN8_OpenDrain (1)                                    /*!< Open drain operation. */


/* Field PIN7: Enables/Disables open drain operation for each [output-configured] IO. */
#define DRV_SX1509_OPENDRAIN_PIN7_Pos       (7)                                    /*!< The position of the field. */
#define DRV_SX1509_OPENDRAIN_PIN7_Msk       (0x1 << DRV_SX1509_OPENDRAIN_PIN7_Pos) /*!< The mask of the field. */
#define DRV_SX1509_OPENDRAIN_PIN7_PushPull  (0)                                    /*!< Regular push-pull operation. */
#define DRV_SX1509_OPENDRAIN_PIN7_OpenDrain (1)                                    /*!< Open drain operation. */


/* Field PIN6: Enables/Disables open drain operation for each [output-configured] IO. */
#define DRV_SX1509_OPENDRAIN_PIN6_Pos       (6)                                    /*!< The position of the field. */
#define DRV_SX1509_OPENDRAIN_PIN6_Msk       (0x1 << DRV_SX1509_OPENDRAIN_PIN6_Pos) /*!< The mask of the field. */
#define DRV_SX1509_OPENDRAIN_PIN6_PushPull  (0)                                    /*!< Regular push-pull operation. */
#define DRV_SX1509_OPENDRAIN_PIN6_OpenDrain (1)                                    /*!< Open drain operation. */


/* Field PIN5: Enables/Disables open drain operation for each [output-configured] IO. */
#define DRV_SX1509_OPENDRAIN_PIN5_Pos       (5)                                    /*!< The position of the field. */
#define DRV_SX1509_OPENDRAIN_PIN5_Msk       (0x1 << DRV_SX1509_OPENDRAIN_PIN5_Pos) /*!< The mask of the field. */
#define DRV_SX1509_OPENDRAIN_PIN5_PushPull  (0)                                    /*!< Regular push-pull operation. */
#define DRV_SX1509_OPENDRAIN_PIN5_OpenDrain (1)                                    /*!< Open drain operation. */


/* Field PIN4: Enables/Disables open drain operation for each [output-configured] IO. */
#define DRV_SX1509_OPENDRAIN_PIN4_Pos       (4)                                    /*!< The position of the field. */
#define DRV_SX1509_OPENDRAIN_PIN4_Msk       (0x1 << DRV_SX1509_OPENDRAIN_PIN4_Pos) /*!< The mask of the field. */
#define DRV_SX1509_OPENDRAIN_PIN4_PushPull  (0)                                    /*!< Regular push-pull operation. */
#define DRV_SX1509_OPENDRAIN_PIN4_OpenDrain (1)                                    /*!< Open drain operation. */


/* Field PIN3: Enables/Disables open drain operation for each [output-configured] IO. */
#define DRV_SX1509_OPENDRAIN_PIN3_Pos       (3)                                    /*!< The position of the field. */
#define DRV_SX1509_OPENDRAIN_PIN3_Msk       (0x1 << DRV_SX1509_OPENDRAIN_PIN3_Pos) /*!< The mask of the field. */
#define DRV_SX1509_OPENDRAIN_PIN3_PushPull  (0)                                    /*!< Regular push-pull operation. */
#define DRV_SX1509_OPENDRAIN_PIN3_OpenDrain (1)                                    /*!< Open drain operation. */


/* Field PIN2: Enables/Disables open drain operation for each [output-configured] IO. */
#define DRV_SX1509_OPENDRAIN_PIN2_Pos       (2)                                    /*!< The position of the field. */
#define DRV_SX1509_OPENDRAIN_PIN2_Msk       (0x1 << DRV_SX1509_OPENDRAIN_PIN2_Pos) /*!< The mask of the field. */
#define DRV_SX1509_OPENDRAIN_PIN2_PushPull  (0)                                    /*!< Regular push-pull operation. */
#define DRV_SX1509_OPENDRAIN_PIN2_OpenDrain (1)                                    /*!< Open drain operation. */


/* Field PIN1: Enables/Disables open drain operation for each [output-configured] IO. */
#define DRV_SX1509_OPENDRAIN_PIN1_Pos       (1)                                    /*!< The position of the field. */
#define DRV_SX1509_OPENDRAIN_PIN1_Msk       (0x1 << DRV_SX1509_OPENDRAIN_PIN1_Pos) /*!< The mask of the field. */
#define DRV_SX1509_OPENDRAIN_PIN1_PushPull  (0)                                    /*!< Regular push-pull operation. */
#define DRV_SX1509_OPENDRAIN_PIN1_OpenDrain (1)                                    /*!< Open drain operation. */


/* Field PIN0: Enables/Disables open drain operation for each [output-configured] IO. */
#define DRV_SX1509_OPENDRAIN_PIN0_Pos       (0)                                    /*!< The position of the field. */
#define DRV_SX1509_OPENDRAIN_PIN0_Msk       (0x1 << DRV_SX1509_OPENDRAIN_PIN0_Pos) /*!< The mask of the field. */
#define DRV_SX1509_OPENDRAIN_PIN0_PushPull  (0)                                    /*!< Regular push-pull operation. */
#define DRV_SX1509_OPENDRAIN_PIN0_OpenDrain (1)                                    /*!< Open drain operation. */


/* Register: POLARITY. */
/* Description: Enables/Disables polarity inversion for each IO. */


/* Field PIN15: Enables/Disables polarity inversion for each IO. */
#define DRV_SX1509_POLARITY_PIN15_Pos      (15)                                   /*!< The position of the field. */
#define DRV_SX1509_POLARITY_PIN15_Msk      (0x1 << DRV_SX1509_POLARITY_PIN15_Pos) /*!< The mask of the field. */
#define DRV_SX1509_POLARITY_PIN15_Normal   (0)                                    /*!< Normal polarity : RegData[x] = IO[x]. */
#define DRV_SX1509_POLARITY_PIN15_Inverted (1)                                    /*!< Inverted polarity : RegData[x] = !IO[x] (for both input and output configured IOs). */


/* Field PIN14: Enables/Disables polarity inversion for each IO. */
#define DRV_SX1509_POLARITY_PIN14_Pos      (14)                                   /*!< The position of the field. */
#define DRV_SX1509_POLARITY_PIN14_Msk      (0x1 << DRV_SX1509_POLARITY_PIN14_Pos) /*!< The mask of the field. */
#define DRV_SX1509_POLARITY_PIN14_Normal   (0)                                    /*!< Normal polarity : RegData[x] = IO[x]. */
#define DRV_SX1509_POLARITY_PIN14_Inverted (1)                                    /*!< Inverted polarity : RegData[x] = !IO[x] (for both input and output configured IOs). */


/* Field PIN13: Enables/Disables polarity inversion for each IO. */
#define DRV_SX1509_POLARITY_PIN13_Pos      (13)                                   /*!< The position of the field. */
#define DRV_SX1509_POLARITY_PIN13_Msk      (0x1 << DRV_SX1509_POLARITY_PIN13_Pos) /*!< The mask of the field. */
#define DRV_SX1509_POLARITY_PIN13_Normal   (0)                                    /*!< Normal polarity : RegData[x] = IO[x]. */
#define DRV_SX1509_POLARITY_PIN13_Inverted (1)                                    /*!< Inverted polarity : RegData[x] = !IO[x] (for both input and output configured IOs). */


/* Field PIN12: Enables/Disables polarity inversion for each IO. */
#define DRV_SX1509_POLARITY_PIN12_Pos      (12)                                   /*!< The position of the field. */
#define DRV_SX1509_POLARITY_PIN12_Msk      (0x1 << DRV_SX1509_POLARITY_PIN12_Pos) /*!< The mask of the field. */
#define DRV_SX1509_POLARITY_PIN12_Normal   (0)                                    /*!< Normal polarity : RegData[x] = IO[x]. */
#define DRV_SX1509_POLARITY_PIN12_Inverted (1)                                    /*!< Inverted polarity : RegData[x] = !IO[x] (for both input and output configured IOs). */


/* Field PIN11: Enables/Disables polarity inversion for each IO. */
#define DRV_SX1509_POLARITY_PIN11_Pos      (11)                                   /*!< The position of the field. */
#define DRV_SX1509_POLARITY_PIN11_Msk      (0x1 << DRV_SX1509_POLARITY_PIN11_Pos) /*!< The mask of the field. */
#define DRV_SX1509_POLARITY_PIN11_Normal   (0)                                    /*!< Normal polarity : RegData[x] = IO[x]. */
#define DRV_SX1509_POLARITY_PIN11_Inverted (1)                                    /*!< Inverted polarity : RegData[x] = !IO[x] (for both input and output configured IOs). */


/* Field PIN10: Enables/Disables polarity inversion for each IO. */
#define DRV_SX1509_POLARITY_PIN10_Pos      (10)                                   /*!< The position of the field. */
#define DRV_SX1509_POLARITY_PIN10_Msk      (0x1 << DRV_SX1509_POLARITY_PIN10_Pos) /*!< The mask of the field. */
#define DRV_SX1509_POLARITY_PIN10_Normal   (0)                                    /*!< Normal polarity : RegData[x] = IO[x]. */
#define DRV_SX1509_POLARITY_PIN10_Inverted (1)                                    /*!< Inverted polarity : RegData[x] = !IO[x] (for both input and output configured IOs). */


/* Field PIN9: Enables/Disables polarity inversion for each IO. */
#define DRV_SX1509_POLARITY_PIN9_Pos      (9)                                   /*!< The position of the field. */
#define DRV_SX1509_POLARITY_PIN9_Msk      (0x1 << DRV_SX1509_POLARITY_PIN9_Pos) /*!< The mask of the field. */
#define DRV_SX1509_POLARITY_PIN9_Normal   (0)                                   /*!< Normal polarity : RegData[x] = IO[x]. */
#define DRV_SX1509_POLARITY_PIN9_Inverted (1)                                   /*!< Inverted polarity : RegData[x] = !IO[x] (for both input and output configured IOs). */


/* Field PIN8: Enables/Disables polarity inversion for each IO. */
#define DRV_SX1509_POLARITY_PIN8_Pos      (8)                                   /*!< The position of the field. */
#define DRV_SX1509_POLARITY_PIN8_Msk      (0x1 << DRV_SX1509_POLARITY_PIN8_Pos) /*!< The mask of the field. */
#define DRV_SX1509_POLARITY_PIN8_Normal   (0)                                   /*!< Normal polarity : RegData[x] = IO[x]. */
#define DRV_SX1509_POLARITY_PIN8_Inverted (1)                                   /*!< Inverted polarity : RegData[x] = !IO[x] (for both input and output configured IOs). */


/* Field PIN7: Enables/Disables polarity inversion for each IO. */
#define DRV_SX1509_POLARITY_PIN7_Pos      (7)                                   /*!< The position of the field. */
#define DRV_SX1509_POLARITY_PIN7_Msk      (0x1 << DRV_SX1509_POLARITY_PIN7_Pos) /*!< The mask of the field. */
#define DRV_SX1509_POLARITY_PIN7_Normal   (0)                                   /*!< Normal polarity : RegData[x] = IO[x]. */
#define DRV_SX1509_POLARITY_PIN7_Inverted (1)                                   /*!< Inverted polarity : RegData[x] = !IO[x] (for both input and output configured IOs). */


/* Field PIN6: Enables/Disables polarity inversion for each IO. */
#define DRV_SX1509_POLARITY_PIN6_Pos      (6)                                   /*!< The position of the field. */
#define DRV_SX1509_POLARITY_PIN6_Msk      (0x1 << DRV_SX1509_POLARITY_PIN6_Pos) /*!< The mask of the field. */
#define DRV_SX1509_POLARITY_PIN6_Normal   (0)                                   /*!< Normal polarity : RegData[x] = IO[x]. */
#define DRV_SX1509_POLARITY_PIN6_Inverted (1)                                   /*!< Inverted polarity : RegData[x] = !IO[x] (for both input and output configured IOs). */


/* Field PIN5: Enables/Disables polarity inversion for each IO. */
#define DRV_SX1509_POLARITY_PIN5_Pos      (5)                                   /*!< The position of the field. */
#define DRV_SX1509_POLARITY_PIN5_Msk      (0x1 << DRV_SX1509_POLARITY_PIN5_Pos) /*!< The mask of the field. */
#define DRV_SX1509_POLARITY_PIN5_Normal   (0)                                   /*!< Normal polarity : RegData[x] = IO[x]. */
#define DRV_SX1509_POLARITY_PIN5_Inverted (1)                                   /*!< Inverted polarity : RegData[x] = !IO[x] (for both input and output configured IOs). */


/* Field PIN4: Enables/Disables polarity inversion for each IO. */
#define DRV_SX1509_POLARITY_PIN4_Pos      (4)                                   /*!< The position of the field. */
#define DRV_SX1509_POLARITY_PIN4_Msk      (0x1 << DRV_SX1509_POLARITY_PIN4_Pos) /*!< The mask of the field. */
#define DRV_SX1509_POLARITY_PIN4_Normal   (0)                                   /*!< Normal polarity : RegData[x] = IO[x]. */
#define DRV_SX1509_POLARITY_PIN4_Inverted (1)                                   /*!< Inverted polarity : RegData[x] = !IO[x] (for both input and output configured IOs). */


/* Field PIN3: Enables/Disables polarity inversion for each IO. */
#define DRV_SX1509_POLARITY_PIN3_Pos      (3)                                   /*!< The position of the field. */
#define DRV_SX1509_POLARITY_PIN3_Msk      (0x1 << DRV_SX1509_POLARITY_PIN3_Pos) /*!< The mask of the field. */
#define DRV_SX1509_POLARITY_PIN3_Normal   (0)                                   /*!< Normal polarity : RegData[x] = IO[x]. */
#define DRV_SX1509_POLARITY_PIN3_Inverted (1)                                   /*!< Inverted polarity : RegData[x] = !IO[x] (for both input and output configured IOs). */


/* Field PIN2: Enables/Disables polarity inversion for each IO. */
#define DRV_SX1509_POLARITY_PIN2_Pos      (2)                                   /*!< The position of the field. */
#define DRV_SX1509_POLARITY_PIN2_Msk      (0x1 << DRV_SX1509_POLARITY_PIN2_Pos) /*!< The mask of the field. */
#define DRV_SX1509_POLARITY_PIN2_Normal   (0)                                   /*!< Normal polarity : RegData[x] = IO[x]. */
#define DRV_SX1509_POLARITY_PIN2_Inverted (1)                                   /*!< Inverted polarity : RegData[x] = !IO[x] (for both input and output configured IOs). */


/* Field PIN1: Enables/Disables polarity inversion for each IO. */
#define DRV_SX1509_POLARITY_PIN1_Pos      (1)                                   /*!< The position of the field. */
#define DRV_SX1509_POLARITY_PIN1_Msk      (0x1 << DRV_SX1509_POLARITY_PIN1_Pos) /*!< The mask of the field. */
#define DRV_SX1509_POLARITY_PIN1_Normal   (0)                                   /*!< Normal polarity : RegData[x] = IO[x]. */
#define DRV_SX1509_POLARITY_PIN1_Inverted (1)                                   /*!< Inverted polarity : RegData[x] = !IO[x] (for both input and output configured IOs). */


/* Field PIN0: Enables/Disables polarity inversion for each IO. */
#define DRV_SX1509_POLARITY_PIN0_Pos      (0)                                   /*!< The position of the field. */
#define DRV_SX1509_POLARITY_PIN0_Msk      (0x1 << DRV_SX1509_POLARITY_PIN0_Pos) /*!< The mask of the field. */
#define DRV_SX1509_POLARITY_PIN0_Normal   (0)                                   /*!< Normal polarity : RegData[x] = IO[x]. */
#define DRV_SX1509_POLARITY_PIN0_Inverted (1)                                   /*!< Inverted polarity : RegData[x] = !IO[x] (for both input and output configured IOs). */


/* Register: DIR. */
/* Description: Configures direction for each IO. */


/* Field PIN15: Configures direction for each IO. */
#define DRV_SX1509_DIR_PIN15_Pos    (15)                              /*!< The position of the field. */
#define DRV_SX1509_DIR_PIN15_Msk    (0x1 << DRV_SX1509_DIR_PIN15_Pos) /*!< The mask of the field. */
#define DRV_SX1509_DIR_PIN15_Output (0)                               /*!< IO is configured as an output. */
#define DRV_SX1509_DIR_PIN15_Input  (1)                               /*!< IO is configured as an input. */


/* Field PIN14: Configures direction for each IO. */
#define DRV_SX1509_DIR_PIN14_Pos    (14)                              /*!< The position of the field. */
#define DRV_SX1509_DIR_PIN14_Msk    (0x1 << DRV_SX1509_DIR_PIN14_Pos) /*!< The mask of the field. */
#define DRV_SX1509_DIR_PIN14_Output (0)                               /*!< IO is configured as an output. */
#define DRV_SX1509_DIR_PIN14_Input  (1)                               /*!< IO is configured as an input. */


/* Field PIN13: Configures direction for each IO. */
#define DRV_SX1509_DIR_PIN13_Pos    (13)                              /*!< The position of the field. */
#define DRV_SX1509_DIR_PIN13_Msk    (0x1 << DRV_SX1509_DIR_PIN13_Pos) /*!< The mask of the field. */
#define DRV_SX1509_DIR_PIN13_Output (0)                               /*!< IO is configured as an output. */
#define DRV_SX1509_DIR_PIN13_Input  (1)                               /*!< IO is configured as an input. */


/* Field PIN12: Configures direction for each IO. */
#define DRV_SX1509_DIR_PIN12_Pos    (12)                              /*!< The position of the field. */
#define DRV_SX1509_DIR_PIN12_Msk    (0x1 << DRV_SX1509_DIR_PIN12_Pos) /*!< The mask of the field. */
#define DRV_SX1509_DIR_PIN12_Output (0)                               /*!< IO is configured as an output. */
#define DRV_SX1509_DIR_PIN12_Input  (1)                               /*!< IO is configured as an input. */


/* Field PIN11: Configures direction for each IO. */
#define DRV_SX1509_DIR_PIN11_Pos    (11)                              /*!< The position of the field. */
#define DRV_SX1509_DIR_PIN11_Msk    (0x1 << DRV_SX1509_DIR_PIN11_Pos) /*!< The mask of the field. */
#define DRV_SX1509_DIR_PIN11_Output (0)                               /*!< IO is configured as an output. */
#define DRV_SX1509_DIR_PIN11_Input  (1)                               /*!< IO is configured as an input. */


/* Field PIN10: Configures direction for each IO. */
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
#define DRV_SX1509_DIR_PIN2_Output (0)                              /*!< IO is configured as an output. */
#define DRV_SX1509_DIR_PIN2_Input  (1)                              /*!< IO is configured as an input. */


/* Field PIN1: Configures direction for each IO. */
#define DRV_SX1509_DIR_PIN1_Pos    (1)                              /*!< The position of the field. */
#define DRV_SX1509_DIR_PIN1_Msk    (0x1 << DRV_SX1509_DIR_PIN1_Pos) /*!< The mask of the field. */
#define DRV_SX1509_DIR_PIN1_Output (0)                              /*!< IO is configured as an output. */
#define DRV_SX1509_DIR_PIN1_Input  (1)                              /*!< IO is configured as an input. */


/* Field PIN0: Configures direction for each IO. */
#define DRV_SX1509_DIR_PIN0_Pos    (0)                              /*!< The position of the field. */
#define DRV_SX1509_DIR_PIN0_Msk    (0x1 << DRV_SX1509_DIR_PIN0_Pos) /*!< The mask of the field. */
#define DRV_SX1509_DIR_PIN0_Output (0)                              /*!< IO is configured as an output. */
#define DRV_SX1509_DIR_PIN0_Input  (1)                              /*!< IO is configured as an input. */


/* Register: DATA. */
/* Description: Data register - I/O. */


/* Field PIN15: Write: Data to be output to the output-configured IOs, Read: Data seen at the IOs, independent of the direction configured.. */
#define DRV_SX1509_DATA_PIN15_Pos  (15)                               /*!< The position of the field. */
#define DRV_SX1509_DATA_PIN15_Msk  (0x1 << DRV_SX1509_DATA_PIN15_Pos) /*!< The mask of the field. */
#define DRV_SX1509_DATA_PIN15_Low  (0)                                /*!< IO is logical low. */
#define DRV_SX1509_DATA_PIN15_High (1)                                /*!< IO is logical high. */


/* Field PIN14: Write: Data to be output to the output-configured IOs, Read: Data seen at the IOs, independent of the direction configured.. */
#define DRV_SX1509_DATA_PIN14_Pos  (14)                               /*!< The position of the field. */
#define DRV_SX1509_DATA_PIN14_Msk  (0x1 << DRV_SX1509_DATA_PIN14_Pos) /*!< The mask of the field. */
#define DRV_SX1509_DATA_PIN14_Low  (0)                                /*!< IO is logical low. */
#define DRV_SX1509_DATA_PIN14_High (1)                                /*!< IO is logical high. */


/* Field PIN13: Write: Data to be output to the output-configured IOs, Read: Data seen at the IOs, independent of the direction configured.. */
#define DRV_SX1509_DATA_PIN13_Pos  (13)                               /*!< The position of the field. */
#define DRV_SX1509_DATA_PIN13_Msk  (0x1 << DRV_SX1509_DATA_PIN13_Pos) /*!< The mask of the field. */
#define DRV_SX1509_DATA_PIN13_Low  (0)                                /*!< IO is logical low. */
#define DRV_SX1509_DATA_PIN13_High (1)                                /*!< IO is logical high. */


/* Field PIN12: Write: Data to be output to the output-configured IOs, Read: Data seen at the IOs, independent of the direction configured.. */
#define DRV_SX1509_DATA_PIN12_Pos  (12)                               /*!< The position of the field. */
#define DRV_SX1509_DATA_PIN12_Msk  (0x1 << DRV_SX1509_DATA_PIN12_Pos) /*!< The mask of the field. */
#define DRV_SX1509_DATA_PIN12_Low  (0)                                /*!< IO is logical low. */
#define DRV_SX1509_DATA_PIN12_High (1)                                /*!< IO is logical high. */


/* Field PIN11: Write: Data to be output to the output-configured IOs, Read: Data seen at the IOs, independent of the direction configured.. */
#define DRV_SX1509_DATA_PIN11_Pos  (11)                               /*!< The position of the field. */
#define DRV_SX1509_DATA_PIN11_Msk  (0x1 << DRV_SX1509_DATA_PIN11_Pos) /*!< The mask of the field. */
#define DRV_SX1509_DATA_PIN11_Low  (0)                                /*!< IO is logical low. */
#define DRV_SX1509_DATA_PIN11_High (1)                                /*!< IO is logical high. */


/* Field PIN10: Write: Data to be output to the output-configured IOs, Read: Data seen at the IOs, independent of the direction configured.. */
#define DRV_SX1509_DATA_PIN10_Pos  (10)                               /*!< The position of the field. */
#define DRV_SX1509_DATA_PIN10_Msk  (0x1 << DRV_SX1509_DATA_PIN10_Pos) /*!< The mask of the field. */
#define DRV_SX1509_DATA_PIN10_Low  (0)                                /*!< IO is logical low. */
#define DRV_SX1509_DATA_PIN10_High (1)                                /*!< IO is logical high. */


/* Field PIN9: Write: Data to be output to the output-configured IOs, Read: Data seen at the IOs, independent of the direction configured.. */
#define DRV_SX1509_DATA_PIN9_Pos  (9)                               /*!< The position of the field. */
#define DRV_SX1509_DATA_PIN9_Msk  (0x1 << DRV_SX1509_DATA_PIN9_Pos) /*!< The mask of the field. */
#define DRV_SX1509_DATA_PIN9_Low  (0)                               /*!< IO is logical low. */
#define DRV_SX1509_DATA_PIN9_High (1)                               /*!< IO is logical high. */


/* Field PIN8: Write: Data to be output to the output-configured IOs, Read: Data seen at the IOs, independent of the direction configured.. */
#define DRV_SX1509_DATA_PIN8_Pos  (8)                               /*!< The position of the field. */
#define DRV_SX1509_DATA_PIN8_Msk  (0x1 << DRV_SX1509_DATA_PIN8_Pos) /*!< The mask of the field. */
#define DRV_SX1509_DATA_PIN8_Low  (0)                               /*!< IO is logical low. */
#define DRV_SX1509_DATA_PIN8_High (1)                               /*!< IO is logical high. */


/* Field PIN7: Write: Data to be output to the output-configured IOs, Read: Data seen at the IOs, independent of the direction configured.. */
#define DRV_SX1509_DATA_PIN7_Pos  (7)                               /*!< The position of the field. */
#define DRV_SX1509_DATA_PIN7_Msk  (0x1 << DRV_SX1509_DATA_PIN7_Pos) /*!< The mask of the field. */
#define DRV_SX1509_DATA_PIN7_Low  (0)                               /*!< IO is logical low. */
#define DRV_SX1509_DATA_PIN7_High (1)                               /*!< IO is logical high. */


/* Field PIN6: Write: Data to be output to the output-configured IOs, Read: Data seen at the IOs, independent of the direction configured.. */
#define DRV_SX1509_DATA_PIN6_Pos  (6)                               /*!< The position of the field. */
#define DRV_SX1509_DATA_PIN6_Msk  (0x1 << DRV_SX1509_DATA_PIN6_Pos) /*!< The mask of the field. */
#define DRV_SX1509_DATA_PIN6_Low  (0)                               /*!< IO is logical low. */
#define DRV_SX1509_DATA_PIN6_High (1)                               /*!< IO is logical high. */


/* Field PIN5: Write: Data to be output to the output-configured IOs, Read: Data seen at the IOs, independent of the direction configured.. */
#define DRV_SX1509_DATA_PIN5_Pos  (5)                               /*!< The position of the field. */
#define DRV_SX1509_DATA_PIN5_Msk  (0x1 << DRV_SX1509_DATA_PIN5_Pos) /*!< The mask of the field. */
#define DRV_SX1509_DATA_PIN5_Low  (0)                               /*!< IO is logical low. */
#define DRV_SX1509_DATA_PIN5_High (1)                               /*!< IO is logical high. */


/* Field PIN4: Write: Data to be output to the output-configured IOs, Read: Data seen at the IOs, independent of the direction configured.. */
#define DRV_SX1509_DATA_PIN4_Pos  (4)                               /*!< The position of the field. */
#define DRV_SX1509_DATA_PIN4_Msk  (0x1 << DRV_SX1509_DATA_PIN4_Pos) /*!< The mask of the field. */
#define DRV_SX1509_DATA_PIN4_Low  (0)                               /*!< IO is logical low. */
#define DRV_SX1509_DATA_PIN4_High (1)                               /*!< IO is logical high. */


/* Field PIN3: Write: Data to be output to the output-configured IOs, Read: Data seen at the IOs, independent of the direction configured.. */
#define DRV_SX1509_DATA_PIN3_Pos  (3)                               /*!< The position of the field. */
#define DRV_SX1509_DATA_PIN3_Msk  (0x1 << DRV_SX1509_DATA_PIN3_Pos) /*!< The mask of the field. */
#define DRV_SX1509_DATA_PIN3_Low  (0)                               /*!< IO is logical low. */
#define DRV_SX1509_DATA_PIN3_High (1)                               /*!< IO is logical high. */


/* Field PIN2: Write: Data to be output to the output-configured IOs, Read: Data seen at the IOs, independent of the direction configured.. */
#define DRV_SX1509_DATA_PIN2_Pos  (2)                               /*!< The position of the field. */
#define DRV_SX1509_DATA_PIN2_Msk  (0x1 << DRV_SX1509_DATA_PIN2_Pos) /*!< The mask of the field. */
#define DRV_SX1509_DATA_PIN2_Low  (0)                               /*!< IO is logical low. */
#define DRV_SX1509_DATA_PIN2_High (1)                               /*!< IO is logical high. */


/* Field PIN1: Write: Data to be output to the output-configured IOs, Read: Data seen at the IOs, independent of the direction configured.. */
#define DRV_SX1509_DATA_PIN1_Pos  (1)                               /*!< The position of the field. */
#define DRV_SX1509_DATA_PIN1_Msk  (0x1 << DRV_SX1509_DATA_PIN1_Pos) /*!< The mask of the field. */
#define DRV_SX1509_DATA_PIN1_Low  (0)                               /*!< IO is logical low. */
#define DRV_SX1509_DATA_PIN1_High (1)                               /*!< IO is logical high. */


/* Field PIN0: Write: Data to be output to the output-configured IOs, Read: Data seen at the IOs, independent of the direction configured.. */
#define DRV_SX1509_DATA_PIN0_Pos  (0)                               /*!< The position of the field. */
#define DRV_SX1509_DATA_PIN0_Msk  (0x1 << DRV_SX1509_DATA_PIN0_Pos) /*!< The mask of the field. */
#define DRV_SX1509_DATA_PIN0_Low  (0)                               /*!< IO is logical low. */
#define DRV_SX1509_DATA_PIN0_High (1)                               /*!< IO is logical high. */


/* Register: INTERRUPTMASK. */
/* Description: Configures which [input-configured] IO will triggeran interrupt on NINT pin. */


/* Field PIN15: Configures which [input-configured] IO will triggeran interrupt on NINT pin. */
#define DRV_SX1509_INTERRUPTMASK_PIN15_Pos      (15)                                        /*!< The position of the field. */
#define DRV_SX1509_INTERRUPTMASK_PIN15_Msk      (0x1 << DRV_SX1509_INTERRUPTMASK_PIN15_Pos) /*!< The mask of the field. */
#define DRV_SX1509_INTERRUPTMASK_PIN15_Unmasked (0)                                         /*!< An event on this IO will trigger an interrupt. */
#define DRV_SX1509_INTERRUPTMASK_PIN15_Masked   (1)                                         /*!< An event on this IO will NOT trigger an interrupt. */


/* Field PIN14: Configures which [input-configured] IO will triggeran interrupt on NINT pin. */
#define DRV_SX1509_INTERRUPTMASK_PIN14_Pos      (14)                                        /*!< The position of the field. */
#define DRV_SX1509_INTERRUPTMASK_PIN14_Msk      (0x1 << DRV_SX1509_INTERRUPTMASK_PIN14_Pos) /*!< The mask of the field. */
#define DRV_SX1509_INTERRUPTMASK_PIN14_Unmasked (0)                                         /*!< An event on this IO will trigger an interrupt. */
#define DRV_SX1509_INTERRUPTMASK_PIN14_Masked   (1)                                         /*!< An event on this IO will NOT trigger an interrupt. */


/* Field PIN13: Configures which [input-configured] IO will triggeran interrupt on NINT pin. */
#define DRV_SX1509_INTERRUPTMASK_PIN13_Pos      (13)                                        /*!< The position of the field. */
#define DRV_SX1509_INTERRUPTMASK_PIN13_Msk      (0x1 << DRV_SX1509_INTERRUPTMASK_PIN13_Pos) /*!< The mask of the field. */
#define DRV_SX1509_INTERRUPTMASK_PIN13_Unmasked (0)                                         /*!< An event on this IO will trigger an interrupt. */
#define DRV_SX1509_INTERRUPTMASK_PIN13_Masked   (1)                                         /*!< An event on this IO will NOT trigger an interrupt. */


/* Field PIN12: Configures which [input-configured] IO will triggeran interrupt on NINT pin. */
#define DRV_SX1509_INTERRUPTMASK_PIN12_Pos      (12)                                        /*!< The position of the field. */
#define DRV_SX1509_INTERRUPTMASK_PIN12_Msk      (0x1 << DRV_SX1509_INTERRUPTMASK_PIN12_Pos) /*!< The mask of the field. */
#define DRV_SX1509_INTERRUPTMASK_PIN12_Unmasked (0)                                         /*!< An event on this IO will trigger an interrupt. */
#define DRV_SX1509_INTERRUPTMASK_PIN12_Masked   (1)                                         /*!< An event on this IO will NOT trigger an interrupt. */


/* Field PIN11: Configures which [input-configured] IO will triggeran interrupt on NINT pin. */
#define DRV_SX1509_INTERRUPTMASK_PIN11_Pos      (11)                                        /*!< The position of the field. */
#define DRV_SX1509_INTERRUPTMASK_PIN11_Msk      (0x1 << DRV_SX1509_INTERRUPTMASK_PIN11_Pos) /*!< The mask of the field. */
#define DRV_SX1509_INTERRUPTMASK_PIN11_Unmasked (0)                                         /*!< An event on this IO will trigger an interrupt. */
#define DRV_SX1509_INTERRUPTMASK_PIN11_Masked   (1)                                         /*!< An event on this IO will NOT trigger an interrupt. */


/* Field PIN10: Configures which [input-configured] IO will triggeran interrupt on NINT pin. */
#define DRV_SX1509_INTERRUPTMASK_PIN10_Pos      (10)                                        /*!< The position of the field. */
#define DRV_SX1509_INTERRUPTMASK_PIN10_Msk      (0x1 << DRV_SX1509_INTERRUPTMASK_PIN10_Pos) /*!< The mask of the field. */
#define DRV_SX1509_INTERRUPTMASK_PIN10_Unmasked (0)                                         /*!< An event on this IO will trigger an interrupt. */
#define DRV_SX1509_INTERRUPTMASK_PIN10_Masked   (1)                                         /*!< An event on this IO will NOT trigger an interrupt. */


/* Field PIN9: Configures which [input-configured] IO will triggeran interrupt on NINT pin. */
#define DRV_SX1509_INTERRUPTMASK_PIN9_Pos      (9)                                        /*!< The position of the field. */
#define DRV_SX1509_INTERRUPTMASK_PIN9_Msk      (0x1 << DRV_SX1509_INTERRUPTMASK_PIN9_Pos) /*!< The mask of the field. */
#define DRV_SX1509_INTERRUPTMASK_PIN9_Unmasked (0)                                        /*!< An event on this IO will trigger an interrupt. */
#define DRV_SX1509_INTERRUPTMASK_PIN9_Masked   (1)                                        /*!< An event on this IO will NOT trigger an interrupt. */


/* Field PIN8: Configures which [input-configured] IO will triggeran interrupt on NINT pin. */
#define DRV_SX1509_INTERRUPTMASK_PIN8_Pos      (8)                                        /*!< The position of the field. */
#define DRV_SX1509_INTERRUPTMASK_PIN8_Msk      (0x1 << DRV_SX1509_INTERRUPTMASK_PIN8_Pos) /*!< The mask of the field. */
#define DRV_SX1509_INTERRUPTMASK_PIN8_Unmasked (0)                                        /*!< An event on this IO will trigger an interrupt. */
#define DRV_SX1509_INTERRUPTMASK_PIN8_Masked   (1)                                        /*!< An event on this IO will NOT trigger an interrupt. */


/* Field PIN7: Configures which [input-configured] IO will triggeran interrupt on NINT pin. */
#define DRV_SX1509_INTERRUPTMASK_PIN7_Pos      (7)                                        /*!< The position of the field. */
#define DRV_SX1509_INTERRUPTMASK_PIN7_Msk      (0x1 << DRV_SX1509_INTERRUPTMASK_PIN7_Pos) /*!< The mask of the field. */
#define DRV_SX1509_INTERRUPTMASK_PIN7_Unmasked (0)                                        /*!< An event on this IO will trigger an interrupt. */
#define DRV_SX1509_INTERRUPTMASK_PIN7_Masked   (1)                                        /*!< An event on this IO will NOT trigger an interrupt. */


/* Field PIN6: Configures which [input-configured] IO will triggeran interrupt on NINT pin. */
#define DRV_SX1509_INTERRUPTMASK_PIN6_Pos      (6)                                        /*!< The position of the field. */
#define DRV_SX1509_INTERRUPTMASK_PIN6_Msk      (0x1 << DRV_SX1509_INTERRUPTMASK_PIN6_Pos) /*!< The mask of the field. */
#define DRV_SX1509_INTERRUPTMASK_PIN6_Unmasked (0)                                        /*!< An event on this IO will trigger an interrupt. */
#define DRV_SX1509_INTERRUPTMASK_PIN6_Masked   (1)                                        /*!< An event on this IO will NOT trigger an interrupt. */


/* Field PIN5: Configures which [input-configured] IO will triggeran interrupt on NINT pin. */
#define DRV_SX1509_INTERRUPTMASK_PIN5_Pos      (5)                                        /*!< The position of the field. */
#define DRV_SX1509_INTERRUPTMASK_PIN5_Msk      (0x1 << DRV_SX1509_INTERRUPTMASK_PIN5_Pos) /*!< The mask of the field. */
#define DRV_SX1509_INTERRUPTMASK_PIN5_Unmasked (0)                                        /*!< An event on this IO will trigger an interrupt. */
#define DRV_SX1509_INTERRUPTMASK_PIN5_Masked   (1)                                        /*!< An event on this IO will NOT trigger an interrupt. */


/* Field PIN4: Configures which [input-configured] IO will triggeran interrupt on NINT pin. */
#define DRV_SX1509_INTERRUPTMASK_PIN4_Pos      (4)                                        /*!< The position of the field. */
#define DRV_SX1509_INTERRUPTMASK_PIN4_Msk      (0x1 << DRV_SX1509_INTERRUPTMASK_PIN4_Pos) /*!< The mask of the field. */
#define DRV_SX1509_INTERRUPTMASK_PIN4_Unmasked (0)                                        /*!< An event on this IO will trigger an interrupt. */
#define DRV_SX1509_INTERRUPTMASK_PIN4_Masked   (1)                                        /*!< An event on this IO will NOT trigger an interrupt. */


/* Field PIN3: Configures which [input-configured] IO will triggeran interrupt on NINT pin. */
#define DRV_SX1509_INTERRUPTMASK_PIN3_Pos      (3)                                        /*!< The position of the field. */
#define DRV_SX1509_INTERRUPTMASK_PIN3_Msk      (0x1 << DRV_SX1509_INTERRUPTMASK_PIN3_Pos) /*!< The mask of the field. */
#define DRV_SX1509_INTERRUPTMASK_PIN3_Unmasked (0)                                        /*!< An event on this IO will trigger an interrupt. */
#define DRV_SX1509_INTERRUPTMASK_PIN3_Masked   (1)                                        /*!< An event on this IO will NOT trigger an interrupt. */


/* Field PIN2: Configures which [input-configured] IO will triggeran interrupt on NINT pin. */
#define DRV_SX1509_INTERRUPTMASK_PIN2_Pos      (2)                                        /*!< The position of the field. */
#define DRV_SX1509_INTERRUPTMASK_PIN2_Msk      (0x1 << DRV_SX1509_INTERRUPTMASK_PIN2_Pos) /*!< The mask of the field. */
#define DRV_SX1509_INTERRUPTMASK_PIN2_Unmasked (0)                                        /*!< An event on this IO will trigger an interrupt. */
#define DRV_SX1509_INTERRUPTMASK_PIN2_Masked   (1)                                        /*!< An event on this IO will NOT trigger an interrupt. */


/* Field PIN1: Configures which [input-configured] IO will triggeran interrupt on NINT pin. */
#define DRV_SX1509_INTERRUPTMASK_PIN1_Pos      (1)                                        /*!< The position of the field. */
#define DRV_SX1509_INTERRUPTMASK_PIN1_Msk      (0x1 << DRV_SX1509_INTERRUPTMASK_PIN1_Pos) /*!< The mask of the field. */
#define DRV_SX1509_INTERRUPTMASK_PIN1_Unmasked (0)                                        /*!< An event on this IO will trigger an interrupt. */
#define DRV_SX1509_INTERRUPTMASK_PIN1_Masked   (1)                                        /*!< An event on this IO will NOT trigger an interrupt. */


/* Field PIN0: Configures which [input-configured] IO will triggeran interrupt on NINT pin. */
#define DRV_SX1509_INTERRUPTMASK_PIN0_Pos      (0)                                        /*!< The position of the field. */
#define DRV_SX1509_INTERRUPTMASK_PIN0_Msk      (0x1 << DRV_SX1509_INTERRUPTMASK_PIN0_Pos) /*!< The mask of the field. */
#define DRV_SX1509_INTERRUPTMASK_PIN0_Unmasked (0)                                        /*!< An event on this IO will trigger an interrupt. */
#define DRV_SX1509_INTERRUPTMASK_PIN0_Masked   (1)                                        /*!< An event on this IO will NOT trigger an interrupt. */


/* Register: SENSE. */
/* Description: Configures edge sensitivity. */


/* Field HIGH15: Configures the edge sensitivity of the corresponting RegData[n]. */
#define DRV_SX1509_SENSE_HIGH15_Pos     (30)                                 /*!< The position of the field. */
#define DRV_SX1509_SENSE_HIGH15_Msk     (0x3 << DRV_SX1509_SENSE_HIGH15_Pos) /*!< The mask of the field. */
#define DRV_SX1509_SENSE_HIGH15_None    (0)                                  /*!< No edge sensitivity configured. */
#define DRV_SX1509_SENSE_HIGH15_Rising  (1)                                  /*!< Sensitive to rising edge. */
#define DRV_SX1509_SENSE_HIGH15_Falling (2)                                  /*!< Sensitive to falling edge. */
#define DRV_SX1509_SENSE_HIGH15_Both    (3)                                  /*!< Sensitive to both edges. */


/* Field HIGH14: Configures the edge sensitivity of the corresponting RegData[n]. */
#define DRV_SX1509_SENSE_HIGH14_Pos     (28)                                 /*!< The position of the field. */
#define DRV_SX1509_SENSE_HIGH14_Msk     (0x3 << DRV_SX1509_SENSE_HIGH14_Pos) /*!< The mask of the field. */
#define DRV_SX1509_SENSE_HIGH14_None    (0)                                  /*!< No edge sensitivity configured. */
#define DRV_SX1509_SENSE_HIGH14_Rising  (1)                                  /*!< Sensitive to rising edge. */
#define DRV_SX1509_SENSE_HIGH14_Falling (2)                                  /*!< Sensitive to falling edge. */
#define DRV_SX1509_SENSE_HIGH14_Both    (3)                                  /*!< Sensitive to both edges. */


/* Field HIGH13: Configures the edge sensitivity of the corresponting RegData[n]. */
#define DRV_SX1509_SENSE_HIGH13_Pos     (26)                                 /*!< The position of the field. */
#define DRV_SX1509_SENSE_HIGH13_Msk     (0x3 << DRV_SX1509_SENSE_HIGH13_Pos) /*!< The mask of the field. */
#define DRV_SX1509_SENSE_HIGH13_None    (0)                                  /*!< No edge sensitivity configured. */
#define DRV_SX1509_SENSE_HIGH13_Rising  (1)                                  /*!< Sensitive to rising edge. */
#define DRV_SX1509_SENSE_HIGH13_Falling (2)                                  /*!< Sensitive to falling edge. */
#define DRV_SX1509_SENSE_HIGH13_Both    (3)                                  /*!< Sensitive to both edges. */


/* Field HIGH12: Configures the edge sensitivity of the corresponting RegData[n]. */
#define DRV_SX1509_SENSE_HIGH12_Pos     (24)                                 /*!< The position of the field. */
#define DRV_SX1509_SENSE_HIGH12_Msk     (0x3 << DRV_SX1509_SENSE_HIGH12_Pos) /*!< The mask of the field. */
#define DRV_SX1509_SENSE_HIGH12_None    (0)                                  /*!< No edge sensitivity configured. */
#define DRV_SX1509_SENSE_HIGH12_Rising  (1)                                  /*!< Sensitive to rising edge. */
#define DRV_SX1509_SENSE_HIGH12_Falling (2)                                  /*!< Sensitive to falling edge. */
#define DRV_SX1509_SENSE_HIGH12_Both    (3)                                  /*!< Sensitive to both edges. */


/* Field LOW11: Configures the edge sensitivity of the corresponting RegData[n]. */
#define DRV_SX1509_SENSE_LOW11_Pos     (22)                                /*!< The position of the field. */
#define DRV_SX1509_SENSE_LOW11_Msk     (0x3 << DRV_SX1509_SENSE_LOW11_Pos) /*!< The mask of the field. */
#define DRV_SX1509_SENSE_LOW11_None    (0)                                 /*!< No edge sensitivity configured. */
#define DRV_SX1509_SENSE_LOW11_Rising  (1)                                 /*!< Sensitive to rising edge. */
#define DRV_SX1509_SENSE_LOW11_Falling (2)                                 /*!< Sensitive to falling edge. */
#define DRV_SX1509_SENSE_LOW11_Both    (3)                                 /*!< Sensitive to both edges. */


/* Field LOW10: Configures the edge sensitivity of the corresponting RegData[n]. */
#define DRV_SX1509_SENSE_LOW10_Pos     (20)                                /*!< The position of the field. */
#define DRV_SX1509_SENSE_LOW10_Msk     (0x3 << DRV_SX1509_SENSE_LOW10_Pos) /*!< The mask of the field. */
#define DRV_SX1509_SENSE_LOW10_None    (0)                                 /*!< No edge sensitivity configured. */
#define DRV_SX1509_SENSE_LOW10_Rising  (1)                                 /*!< Sensitive to rising edge. */
#define DRV_SX1509_SENSE_LOW10_Falling (2)                                 /*!< Sensitive to falling edge. */
#define DRV_SX1509_SENSE_LOW10_Both    (3)                                 /*!< Sensitive to both edges. */


/* Field LOW9: Configures the edge sensitivity of the corresponting RegData[n]. */
#define DRV_SX1509_SENSE_LOW9_Pos     (18)                               /*!< The position of the field. */
#define DRV_SX1509_SENSE_LOW9_Msk     (0x3 << DRV_SX1509_SENSE_LOW9_Pos) /*!< The mask of the field. */
#define DRV_SX1509_SENSE_LOW9_None    (0)                                /*!< No edge sensitivity configured. */
#define DRV_SX1509_SENSE_LOW9_Rising  (1)                                /*!< Sensitive to rising edge. */
#define DRV_SX1509_SENSE_LOW9_Falling (2)                                /*!< Sensitive to falling edge. */
#define DRV_SX1509_SENSE_LOW9_Both    (3)                                /*!< Sensitive to both edges. */


/* Field LOW8: Configures the edge sensitivity of the corresponting RegData[n]. */
#define DRV_SX1509_SENSE_LOW8_Pos     (16)                               /*!< The position of the field. */
#define DRV_SX1509_SENSE_LOW8_Msk     (0x3 << DRV_SX1509_SENSE_LOW8_Pos) /*!< The mask of the field. */
#define DRV_SX1509_SENSE_LOW8_None    (0)                                /*!< No edge sensitivity configured. */
#define DRV_SX1509_SENSE_LOW8_Rising  (1)                                /*!< Sensitive to rising edge. */
#define DRV_SX1509_SENSE_LOW8_Falling (2)                                /*!< Sensitive to falling edge. */
#define DRV_SX1509_SENSE_LOW8_Both    (3)                                /*!< Sensitive to both edges. */


/* Field HIGH7: Configures the edge sensitivity of the corresponting RegData[n]. */
#define DRV_SX1509_SENSE_HIGH7_Pos     (14)                                /*!< The position of the field. */
#define DRV_SX1509_SENSE_HIGH7_Msk     (0x3 << DRV_SX1509_SENSE_HIGH7_Pos) /*!< The mask of the field. */
#define DRV_SX1509_SENSE_HIGH7_None    (0)                                 /*!< No edge sensitivity configured. */
#define DRV_SX1509_SENSE_HIGH7_Rising  (1)                                 /*!< Sensitive to rising edge. */
#define DRV_SX1509_SENSE_HIGH7_Falling (2)                                 /*!< Sensitive to falling edge. */
#define DRV_SX1509_SENSE_HIGH7_Both    (3)                                 /*!< Sensitive to both edges. */


/* Field HIGH6: Configures the edge sensitivity of the corresponting RegData[n]. */
#define DRV_SX1509_SENSE_HIGH6_Pos     (12)                                /*!< The position of the field. */
#define DRV_SX1509_SENSE_HIGH6_Msk     (0x3 << DRV_SX1509_SENSE_HIGH6_Pos) /*!< The mask of the field. */
#define DRV_SX1509_SENSE_HIGH6_None    (0)                                 /*!< No edge sensitivity configured. */
#define DRV_SX1509_SENSE_HIGH6_Rising  (1)                                 /*!< Sensitive to rising edge. */
#define DRV_SX1509_SENSE_HIGH6_Falling (2)                                 /*!< Sensitive to falling edge. */
#define DRV_SX1509_SENSE_HIGH6_Both    (3)                                 /*!< Sensitive to both edges. */


/* Field HIGH5: Configures the edge sensitivity of the corresponting RegData[n]. */
#define DRV_SX1509_SENSE_HIGH5_Pos     (10)                                /*!< The position of the field. */
#define DRV_SX1509_SENSE_HIGH5_Msk     (0x3 << DRV_SX1509_SENSE_HIGH5_Pos) /*!< The mask of the field. */
#define DRV_SX1509_SENSE_HIGH5_None    (0)                                 /*!< No edge sensitivity configured. */
#define DRV_SX1509_SENSE_HIGH5_Rising  (1)                                 /*!< Sensitive to rising edge. */
#define DRV_SX1509_SENSE_HIGH5_Falling (2)                                 /*!< Sensitive to falling edge. */
#define DRV_SX1509_SENSE_HIGH5_Both    (3)                                 /*!< Sensitive to both edges. */


/* Field HIGH4: Configures the edge sensitivity of the corresponting RegData[n]. */
#define DRV_SX1509_SENSE_HIGH4_Pos     (8)                                 /*!< The position of the field. */
#define DRV_SX1509_SENSE_HIGH4_Msk     (0x3 << DRV_SX1509_SENSE_HIGH4_Pos) /*!< The mask of the field. */
#define DRV_SX1509_SENSE_HIGH4_None    (0)                                 /*!< No edge sensitivity configured. */
#define DRV_SX1509_SENSE_HIGH4_Rising  (1)                                 /*!< Sensitive to rising edge. */
#define DRV_SX1509_SENSE_HIGH4_Falling (2)                                 /*!< Sensitive to falling edge. */
#define DRV_SX1509_SENSE_HIGH4_Both    (3)                                 /*!< Sensitive to both edges. */


/* Field LOW3: Configures the edge sensitivity of the corresponting RegData[n]. */
#define DRV_SX1509_SENSE_LOW3_Pos     (6)                                /*!< The position of the field. */
#define DRV_SX1509_SENSE_LOW3_Msk     (0x3 << DRV_SX1509_SENSE_LOW3_Pos) /*!< The mask of the field. */
#define DRV_SX1509_SENSE_LOW3_None    (0)                                /*!< No edge sensitivity configured. */
#define DRV_SX1509_SENSE_LOW3_Rising  (1)                                /*!< Sensitive to rising edge. */
#define DRV_SX1509_SENSE_LOW3_Falling (2)                                /*!< Sensitive to falling edge. */
#define DRV_SX1509_SENSE_LOW3_Both    (3)                                /*!< Sensitive to both edges. */


/* Field LOW2: Configures the edge sensitivity of the corresponting RegData[n]. */
#define DRV_SX1509_SENSE_LOW2_Pos     (4)                                /*!< The position of the field. */
#define DRV_SX1509_SENSE_LOW2_Msk     (0x3 << DRV_SX1509_SENSE_LOW2_Pos) /*!< The mask of the field. */
#define DRV_SX1509_SENSE_LOW2_None    (0)                                /*!< No edge sensitivity configured. */
#define DRV_SX1509_SENSE_LOW2_Rising  (1)                                /*!< Sensitive to rising edge. */
#define DRV_SX1509_SENSE_LOW2_Falling (2)                                /*!< Sensitive to falling edge. */
#define DRV_SX1509_SENSE_LOW2_Both    (3)                                /*!< Sensitive to both edges. */


/* Field LOW1: Configures the edge sensitivity of the corresponting RegData[n]. */
#define DRV_SX1509_SENSE_LOW1_Pos     (2)                                /*!< The position of the field. */
#define DRV_SX1509_SENSE_LOW1_Msk     (0x3 << DRV_SX1509_SENSE_LOW1_Pos) /*!< The mask of the field. */
#define DRV_SX1509_SENSE_LOW1_None    (0)                                /*!< No edge sensitivity configured. */
#define DRV_SX1509_SENSE_LOW1_Rising  (1)                                /*!< Sensitive to rising edge. */
#define DRV_SX1509_SENSE_LOW1_Falling (2)                                /*!< Sensitive to falling edge. */
#define DRV_SX1509_SENSE_LOW1_Both    (3)                                /*!< Sensitive to both edges. */


/* Field LOW0: Configures the edge sensitivity of the corresponting RegData[n]. */
#define DRV_SX1509_SENSE_LOW0_Pos     (0)                                /*!< The position of the field. */
#define DRV_SX1509_SENSE_LOW0_Msk     (0x3 << DRV_SX1509_SENSE_LOW0_Pos) /*!< The mask of the field. */
#define DRV_SX1509_SENSE_LOW0_None    (0)                                /*!< No edge sensitivity configured. */
#define DRV_SX1509_SENSE_LOW0_Rising  (1)                                /*!< Sensitive to rising edge. */
#define DRV_SX1509_SENSE_LOW0_Falling (2)                                /*!< Sensitive to falling edge. */
#define DRV_SX1509_SENSE_LOW0_Both    (3)                                /*!< Sensitive to both edges. */


/* Register: INTERRUPTSOURCE. */
/* Description: Interrupt source register - I/O. */


/* Field PIN15: Interrupt source (from IOs set in RegInterruptMask). */
#define DRV_SX1509_INTERRUPTSOURCE_PIN15_Pos       (15)                                          /*!< The position of the field. */
#define DRV_SX1509_INTERRUPTSOURCE_PIN15_Msk       (0x1 << DRV_SX1509_INTERRUPTSOURCE_PIN15_Pos) /*!< The mask of the field. */
#define DRV_SX1509_INTERRUPTSOURCE_PIN15_None      (0)                                           /*!< No interrupt has been triggered by this IO. */
#define DRV_SX1509_INTERRUPTSOURCE_PIN15_Triggered (1)                                           /*!< An interrupt has been triggered by this IO (an event as configured in relevant RegSense register occured).. */


/* Field PIN14: Interrupt source (from IOs set in RegInterruptMask). */
#define DRV_SX1509_INTERRUPTSOURCE_PIN14_Pos       (14)                                          /*!< The position of the field. */
#define DRV_SX1509_INTERRUPTSOURCE_PIN14_Msk       (0x1 << DRV_SX1509_INTERRUPTSOURCE_PIN14_Pos) /*!< The mask of the field. */
#define DRV_SX1509_INTERRUPTSOURCE_PIN14_None      (0)                                           /*!< No interrupt has been triggered by this IO. */
#define DRV_SX1509_INTERRUPTSOURCE_PIN14_Triggered (1)                                           /*!< An interrupt has been triggered by this IO (an event as configured in relevant RegSense register occured).. */


/* Field PIN13: Interrupt source (from IOs set in RegInterruptMask). */
#define DRV_SX1509_INTERRUPTSOURCE_PIN13_Pos       (13)                                          /*!< The position of the field. */
#define DRV_SX1509_INTERRUPTSOURCE_PIN13_Msk       (0x1 << DRV_SX1509_INTERRUPTSOURCE_PIN13_Pos) /*!< The mask of the field. */
#define DRV_SX1509_INTERRUPTSOURCE_PIN13_None      (0)                                           /*!< No interrupt has been triggered by this IO. */
#define DRV_SX1509_INTERRUPTSOURCE_PIN13_Triggered (1)                                           /*!< An interrupt has been triggered by this IO (an event as configured in relevant RegSense register occured).. */


/* Field PIN12: Interrupt source (from IOs set in RegInterruptMask). */
#define DRV_SX1509_INTERRUPTSOURCE_PIN12_Pos       (12)                                          /*!< The position of the field. */
#define DRV_SX1509_INTERRUPTSOURCE_PIN12_Msk       (0x1 << DRV_SX1509_INTERRUPTSOURCE_PIN12_Pos) /*!< The mask of the field. */
#define DRV_SX1509_INTERRUPTSOURCE_PIN12_None      (0)                                           /*!< No interrupt has been triggered by this IO. */
#define DRV_SX1509_INTERRUPTSOURCE_PIN12_Triggered (1)                                           /*!< An interrupt has been triggered by this IO (an event as configured in relevant RegSense register occured).. */


/* Field PIN11: Interrupt source (from IOs set in RegInterruptMask). */
#define DRV_SX1509_INTERRUPTSOURCE_PIN11_Pos       (11)                                          /*!< The position of the field. */
#define DRV_SX1509_INTERRUPTSOURCE_PIN11_Msk       (0x1 << DRV_SX1509_INTERRUPTSOURCE_PIN11_Pos) /*!< The mask of the field. */
#define DRV_SX1509_INTERRUPTSOURCE_PIN11_None      (0)                                           /*!< No interrupt has been triggered by this IO. */
#define DRV_SX1509_INTERRUPTSOURCE_PIN11_Triggered (1)                                           /*!< An interrupt has been triggered by this IO (an event as configured in relevant RegSense register occured).. */


/* Field PIN10: Interrupt source (from IOs set in RegInterruptMask). */
#define DRV_SX1509_INTERRUPTSOURCE_PIN10_Pos       (10)                                          /*!< The position of the field. */
#define DRV_SX1509_INTERRUPTSOURCE_PIN10_Msk       (0x1 << DRV_SX1509_INTERRUPTSOURCE_PIN10_Pos) /*!< The mask of the field. */
#define DRV_SX1509_INTERRUPTSOURCE_PIN10_None      (0)                                           /*!< No interrupt has been triggered by this IO. */
#define DRV_SX1509_INTERRUPTSOURCE_PIN10_Triggered (1)                                           /*!< An interrupt has been triggered by this IO (an event as configured in relevant RegSense register occured).. */


/* Field PIN9: Interrupt source (from IOs set in RegInterruptMask). */
#define DRV_SX1509_INTERRUPTSOURCE_PIN9_Pos       (9)                                          /*!< The position of the field. */
#define DRV_SX1509_INTERRUPTSOURCE_PIN9_Msk       (0x1 << DRV_SX1509_INTERRUPTSOURCE_PIN9_Pos) /*!< The mask of the field. */
#define DRV_SX1509_INTERRUPTSOURCE_PIN9_None      (0)                                          /*!< No interrupt has been triggered by this IO. */
#define DRV_SX1509_INTERRUPTSOURCE_PIN9_Triggered (1)                                          /*!< An interrupt has been triggered by this IO (an event as configured in relevant RegSense register occured).. */


/* Field PIN8: Interrupt source (from IOs set in RegInterruptMask). */
#define DRV_SX1509_INTERRUPTSOURCE_PIN8_Pos       (8)                                          /*!< The position of the field. */
#define DRV_SX1509_INTERRUPTSOURCE_PIN8_Msk       (0x1 << DRV_SX1509_INTERRUPTSOURCE_PIN8_Pos) /*!< The mask of the field. */
#define DRV_SX1509_INTERRUPTSOURCE_PIN8_None      (0)                                          /*!< No interrupt has been triggered by this IO. */
#define DRV_SX1509_INTERRUPTSOURCE_PIN8_Triggered (1)                                          /*!< An interrupt has been triggered by this IO (an event as configured in relevant RegSense register occured).. */


/* Field PIN7: Interrupt source (from IOs set in RegInterruptMask). */
#define DRV_SX1509_INTERRUPTSOURCE_PIN7_Pos       (7)                                          /*!< The position of the field. */
#define DRV_SX1509_INTERRUPTSOURCE_PIN7_Msk       (0x1 << DRV_SX1509_INTERRUPTSOURCE_PIN7_Pos) /*!< The mask of the field. */
#define DRV_SX1509_INTERRUPTSOURCE_PIN7_None      (0)                                          /*!< No interrupt has been triggered by this IO. */
#define DRV_SX1509_INTERRUPTSOURCE_PIN7_Triggered (1)                                          /*!< An interrupt has been triggered by this IO (an event as configured in relevant RegSense register occured).. */


/* Field PIN6: Interrupt source (from IOs set in RegInterruptMask). */
#define DRV_SX1509_INTERRUPTSOURCE_PIN6_Pos       (6)                                          /*!< The position of the field. */
#define DRV_SX1509_INTERRUPTSOURCE_PIN6_Msk       (0x1 << DRV_SX1509_INTERRUPTSOURCE_PIN6_Pos) /*!< The mask of the field. */
#define DRV_SX1509_INTERRUPTSOURCE_PIN6_None      (0)                                          /*!< No interrupt has been triggered by this IO. */
#define DRV_SX1509_INTERRUPTSOURCE_PIN6_Triggered (1)                                          /*!< An interrupt has been triggered by this IO (an event as configured in relevant RegSense register occured).. */


/* Field PIN5: Interrupt source (from IOs set in RegInterruptMask). */
#define DRV_SX1509_INTERRUPTSOURCE_PIN5_Pos       (5)                                          /*!< The position of the field. */
#define DRV_SX1509_INTERRUPTSOURCE_PIN5_Msk       (0x1 << DRV_SX1509_INTERRUPTSOURCE_PIN5_Pos) /*!< The mask of the field. */
#define DRV_SX1509_INTERRUPTSOURCE_PIN5_None      (0)                                          /*!< No interrupt has been triggered by this IO. */
#define DRV_SX1509_INTERRUPTSOURCE_PIN5_Triggered (1)                                          /*!< An interrupt has been triggered by this IO (an event as configured in relevant RegSense register occured).. */


/* Field PIN4: Interrupt source (from IOs set in RegInterruptMask). */
#define DRV_SX1509_INTERRUPTSOURCE_PIN4_Pos       (4)                                          /*!< The position of the field. */
#define DRV_SX1509_INTERRUPTSOURCE_PIN4_Msk       (0x1 << DRV_SX1509_INTERRUPTSOURCE_PIN4_Pos) /*!< The mask of the field. */
#define DRV_SX1509_INTERRUPTSOURCE_PIN4_None      (0)                                          /*!< No interrupt has been triggered by this IO. */
#define DRV_SX1509_INTERRUPTSOURCE_PIN4_Triggered (1)                                          /*!< An interrupt has been triggered by this IO (an event as configured in relevant RegSense register occured).. */


/* Field PIN3: Interrupt source (from IOs set in RegInterruptMask). */
#define DRV_SX1509_INTERRUPTSOURCE_PIN3_Pos       (3)                                          /*!< The position of the field. */
#define DRV_SX1509_INTERRUPTSOURCE_PIN3_Msk       (0x1 << DRV_SX1509_INTERRUPTSOURCE_PIN3_Pos) /*!< The mask of the field. */
#define DRV_SX1509_INTERRUPTSOURCE_PIN3_None      (0)                                          /*!< No interrupt has been triggered by this IO. */
#define DRV_SX1509_INTERRUPTSOURCE_PIN3_Triggered (1)                                          /*!< An interrupt has been triggered by this IO (an event as configured in relevant RegSense register occured).. */


/* Field PIN2: Interrupt source (from IOs set in RegInterruptMask). */
#define DRV_SX1509_INTERRUPTSOURCE_PIN2_Pos       (2)                                          /*!< The position of the field. */
#define DRV_SX1509_INTERRUPTSOURCE_PIN2_Msk       (0x1 << DRV_SX1509_INTERRUPTSOURCE_PIN2_Pos) /*!< The mask of the field. */
#define DRV_SX1509_INTERRUPTSOURCE_PIN2_None      (0)                                          /*!< No interrupt has been triggered by this IO. */
#define DRV_SX1509_INTERRUPTSOURCE_PIN2_Triggered (1)                                          /*!< An interrupt has been triggered by this IO (an event as configured in relevant RegSense register occured).. */


/* Field PIN1: Interrupt source (from IOs set in RegInterruptMask). */
#define DRV_SX1509_INTERRUPTSOURCE_PIN1_Pos       (1)                                          /*!< The position of the field. */
#define DRV_SX1509_INTERRUPTSOURCE_PIN1_Msk       (0x1 << DRV_SX1509_INTERRUPTSOURCE_PIN1_Pos) /*!< The mask of the field. */
#define DRV_SX1509_INTERRUPTSOURCE_PIN1_None      (0)                                          /*!< No interrupt has been triggered by this IO. */
#define DRV_SX1509_INTERRUPTSOURCE_PIN1_Triggered (1)                                          /*!< An interrupt has been triggered by this IO (an event as configured in relevant RegSense register occured).. */


/* Field PIN0: Interrupt source (from IOs set in RegInterruptMask). */
#define DRV_SX1509_INTERRUPTSOURCE_PIN0_Pos       (0)                                          /*!< The position of the field. */
#define DRV_SX1509_INTERRUPTSOURCE_PIN0_Msk       (0x1 << DRV_SX1509_INTERRUPTSOURCE_PIN0_Pos) /*!< The mask of the field. */
#define DRV_SX1509_INTERRUPTSOURCE_PIN0_None      (0)                                          /*!< No interrupt has been triggered by this IO. */
#define DRV_SX1509_INTERRUPTSOURCE_PIN0_Triggered (1)                                          /*!< An interrupt has been triggered by this IO (an event as configured in relevant RegSense register occured).. */


/* Register: EVENTSTATUS. */
/* Description: Event status register - I/O. */


/* Field PIN15: Interrupt source (from IOs set in RegInterruptMask). */
#define DRV_SX1509_EVENTSTATUS_PIN15_Pos       (15)                                      /*!< The position of the field. */
#define DRV_SX1509_EVENTSTATUS_PIN15_Msk       (0x1 << DRV_SX1509_EVENTSTATUS_PIN15_Pos) /*!< The mask of the field. */
#define DRV_SX1509_EVENTSTATUS_PIN15_None      (0)                                       /*!< No event has occured on this IO. */
#define DRV_SX1509_EVENTSTATUS_PIN15_Triggered (1)                                       /*!< An event has occured on this IO (an edge as configured in relevant RegSense register occured). */


/* Field PIN14: Interrupt source (from IOs set in RegInterruptMask). */
#define DRV_SX1509_EVENTSTATUS_PIN14_Pos       (14)                                      /*!< The position of the field. */
#define DRV_SX1509_EVENTSTATUS_PIN14_Msk       (0x1 << DRV_SX1509_EVENTSTATUS_PIN14_Pos) /*!< The mask of the field. */
#define DRV_SX1509_EVENTSTATUS_PIN14_None      (0)                                       /*!< No event has occured on this IO. */
#define DRV_SX1509_EVENTSTATUS_PIN14_Triggered (1)                                       /*!< An event has occured on this IO (an edge as configured in relevant RegSense register occured). */


/* Field PIN13: Interrupt source (from IOs set in RegInterruptMask). */
#define DRV_SX1509_EVENTSTATUS_PIN13_Pos       (13)                                      /*!< The position of the field. */
#define DRV_SX1509_EVENTSTATUS_PIN13_Msk       (0x1 << DRV_SX1509_EVENTSTATUS_PIN13_Pos) /*!< The mask of the field. */
#define DRV_SX1509_EVENTSTATUS_PIN13_None      (0)                                       /*!< No event has occured on this IO. */
#define DRV_SX1509_EVENTSTATUS_PIN13_Triggered (1)                                       /*!< An event has occured on this IO (an edge as configured in relevant RegSense register occured). */


/* Field PIN12: Interrupt source (from IOs set in RegInterruptMask). */
#define DRV_SX1509_EVENTSTATUS_PIN12_Pos       (12)                                      /*!< The position of the field. */
#define DRV_SX1509_EVENTSTATUS_PIN12_Msk       (0x1 << DRV_SX1509_EVENTSTATUS_PIN12_Pos) /*!< The mask of the field. */
#define DRV_SX1509_EVENTSTATUS_PIN12_None      (0)                                       /*!< No event has occured on this IO. */
#define DRV_SX1509_EVENTSTATUS_PIN12_Triggered (1)                                       /*!< An event has occured on this IO (an edge as configured in relevant RegSense register occured). */


/* Field PIN11: Interrupt source (from IOs set in RegInterruptMask). */
#define DRV_SX1509_EVENTSTATUS_PIN11_Pos       (11)                                      /*!< The position of the field. */
#define DRV_SX1509_EVENTSTATUS_PIN11_Msk       (0x1 << DRV_SX1509_EVENTSTATUS_PIN11_Pos) /*!< The mask of the field. */
#define DRV_SX1509_EVENTSTATUS_PIN11_None      (0)                                       /*!< No event has occured on this IO. */
#define DRV_SX1509_EVENTSTATUS_PIN11_Triggered (1)                                       /*!< An event has occured on this IO (an edge as configured in relevant RegSense register occured). */
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
